ristllin/Nimbus/DISCLAIMER.md

# Disclaimer

Nimbus is a hobbyist, do-it-yourself hardware and firmware project. It is
provided **"as is", without warranty of any kind**, express or implied,
including but not limited to fitness for a particular purpose, merchantability,
and non-infringement. This document supplements, and does not replace, the
warranty and liability disclaimers in [LICENSE](LICENSE) and
[LICENSE-docs](LICENSE-docs).

**By building, modifying, powering, or using a device based on this project,
you accept full and sole responsibility for the result.** The author and
contributors are not liable for any damage, loss, or injury of any kind
arising from the construction or use of hardware or software described here,
including damage to property, data loss, fire, or personal injury.

## Electrical and battery safety

This project describes wiring mains-powered USB supplies, DC-DC converters,
LED loads, and **lithium-ion battery packs (2S 18650)**. Lithium-ion cells can
overheat, vent, catch fire, or explode if they are damaged, short-circuited,
over-charged, over-discharged, punctured, or charged unattended with
inadequate protection.

If you choose to build a battery-powered variant, you do so entirely at your
own risk. At minimum: use quality cells from a reputable supplier, always use
a proper 2S protection/balance board (BMS), fuse the pack, never leave a
charging pack unattended, never exceed component voltage or current ratings,
and stop immediately if anything becomes hot. If you are not comfortable and
experienced with battery wiring, build the USB-powered variant instead, or do
not build the project at all.

## Not a certified product

Devices you build from these files are self-built prototypes, not tested or
certified consumer products. They carry no CE/FCC/UKCA or other regulatory
approval. You are responsible for compliance with all laws, regulations, and
safety standards that apply to you, including those covering radio equipment
(Wi-Fi/Bluetooth), electrical safety, and battery transport and disposal in
your jurisdiction.

## Documentation accuracy

The documentation is provided in good faith and may contain errors or become
outdated. Nothing in it is professional engineering, safety, or legal advice.
Verify everything against your own components before powering anything.
