ristllin/Nimbus/docs/ota.md

# OTA firmware updates

> This page is the OTA design and device-behavior reference. The operator
> runbook - how to cut a release, which tokens expire where and how to renew
> them, and how to rotate the signing key - is maintainer-internal and is not
> part of the public docs.

Nimbus updates itself over Wi-Fi from GitHub Releases. The flash layout was
already A/B (stock `default_16MB.csv`: `otadata` + two 6.5 MB app slots), so OTA
needed no partition change: the running slot downloads the new image into the
**inactive** slot, verifies it, flips the boot flag, restarts - and **rolls back
by itself** if the new firmware can't boot.

⚠ **Delivery is from the dedicated releases repo [`ristllin/nimbus-fw-releases`](https://github.com/ristllin/nimbus-fw-releases), NOT the source repo.** The device
downloads over unauthenticated HTTPS (no repo credentials baked into firmware),
so release assets must live somewhere any device can fetch them - a dedicated,
assets-only public repo (the same pattern as the SFX assets). The signed
binaries carry no secrets, and the ECDSA signature is what devices trust.
Forking the project and shipping to your own devices? See
[`self-hosted-ota.md`](self-hosted-ota.md).

```mermaid
flowchart TD
  TAG["tag vX.Y.Z on Nimbus<br/>(source repo)"] --> CI["release.yml<br/>build nimbus-tft + freenove images<br/>sign typed manifest (ECDSA)<br/>publish images + per-variant web-flash"]
  CI --> REL["Release on nimbus-fw-releases<br/>(PUBLIC delivery repo)"]
  REL -->|"GET /releases/latest/download/manifest.json<br/>302 → objects.githubusercontent.com (followed)"| GET
  subgraph DEV["device (daily / button)"]
    GET["fetch manifest"] --> CMP["compare versions → notify / 1-click install"]
    CMP --> DL["stream .bin → INACTIVE slot (+SHA-256)"]
    DL --> VER["verify SHA + signature<br/>(anchors: include/ota_pubkey.h)"]
    VER --> FLIP["arm NVS guard → flip otadata → restart"]
    FLIP --> OK["healthy 120 s → mark valid ('ok vX')"]
    FLIP --> RB["3 failed boots → flip back ('rollback vX')"]
  end
```

## Trust model

- **Signature** (the real gate): CI signs, per variant, the canonical message
  `nimbus-ota-v2\n<version>\n<type>\n<sha256-hex>\n` with ECDSA P-256
  (secret `OTA_SIGNING_KEY`). The device rebuilds that message from what it
  actually downloaded and verifies against the public keys baked into
  [`include/ota_pubkey.h`](../include/ota_pubkey.h) **before** the boot flag
  flips. Binding version+type kills mix-and-match and cross-version replay. (The
  schema-1 transition is over: `release.yml` publishes only the typed schema-2
  manifest and `parseManifest()` rejects anything else, so the legacy
  `nimbus-ota-v1` message is no longer signed - see Typed manifests.)
- **TLS**: downloads ride `tlsSetup()` (CA-bundle validation, `tlsVerify`
  default ON), so the transport is also authenticated on default settings.
- **Residual**: a MITM against a `tlsVerify=0` device can only replay an old
  *genuinely signed* release; auto-install moves strictly forward in version,
  so the worst case is pinning a device at its current version. Manual
  downgrade needs the authenticated web UI + `force`.
- The `test` variant additionally trusts a COMMITTED test key
  (`test/ota_test_key.pem`, `#ifdef NIMBUS_TEST` only) so the HIL suite can
  sign fixtures. Never flash `env:test` on a production unit.

## Typed manifests (v2)

The manifest is **typed**: `schema: 2`, and each entry in `variants` is keyed on
the device **type**, not the build tag. The four types are frozen:
`nimbus-tft` (the TFT + ring board), and `freenove-28` / `freenove-35` /
`freenove-40` (the all-in-one touchscreen, by panel size). A release publishes one
`manifest.json` holding every type that has an image; a device looks up only its
own type.

```
{ "schema": 2, "version": "v4.3.0", "notes": "...",
  "variants": {
    "nimbus-tft":  { "url": "...", "size": 3600000, "sha256": "...", "sig": "..." },
    "freenove-28": { "url": "...", "size": 3600000, "sha256": "...", "sig": "..." },
    "freenove-35": { ... }, "freenove-40": { ... } } }
```

- **Where the type comes from**: NVS key `otaType`, seeded by the flasher on a
  fresh install or written by the transition release on an existing device. If it
  is unset, the build falls back to its compile-time tag so dev/HIL builds
  (`test`/`test-cyd`) still resolve. A stored type from the wrong board family is
  refused (a Solide build only accepts `nimbus-tft`, a Freenove build only the
  `freenove-*` sizes), so a mis-seeded NVS can never pull a wrong-pinout image -
  the runtime twin of the compile-time board/variant bind in `ota_update.cpp`.
- **Untyped devices get no update**: a device whose type is empty (or absent from
  the manifest) matches no variant and reports "no update" - a settled state, not
  an error. **E-ink devices are frozen this way**: they carry no type, so after
  the transition release they never install again, and the final e-ink image reads
  "Updates have ended for this board."
- **The transition release** is a final **schema-1** manifest published under the
  tag existing firmware polls. Fielded firmware matches it by its build tag
  (`esp32s3`/`cyd`) and installs it; on first boot the new image derives its type
  from `scrModel` + board and persists `otaType`, then uses the schema-2 manifest
  thereafter. Generate it with `tools/make_manifest.py --schema 1`; the typed
  releases use the default `--schema 2`.
- **Derivation only guesses a single-type family.** A Solide + TFT board derives
  `nimbus-tft` (the Solide family has exactly one type). A Freenove has three sizes
  (`freenove-28` / `-35` / `-40`) that board identity cannot tell apart, so an
  UNSEEDED Freenove derives no type and is offered no update: it must be reflashed
  with its explicit size rather than guessing one. The flasher seeds the exact size
  on every real install, so this only ever refuses a Freenove that reached the typed
  scheme with no seed.

The repo-layout decision (reuse `nimbus-fw-releases`, one manifest per release) is
recorded in [`adr/0001-ota-releases-repo.md`](adr/0001-ota-releases-repo.md).

## Cutting a release

Publishing a signed release to the fleet - the version bump and tag, the CI
signing step, the one-time schema-1 transition manifest, the two CI secrets
(`OTA_SIGNING_KEY` and `RELEASE_PAT`), and token/key renewal and rotation - is an
operator task. That runbook is maintainer-internal and is not part of the public
docs. What a device does with a release once it is published is described below.

## Release tags: firmware and Virtual Nimbus image

One release workflow serves two channels, and the tag that is pushed picks the channel.
They are controlled separately: a Virtual Nimbus image can ship without a firmware OTA
release, and no release moves running Virtual Nimbus instances by itself.

| Tag | Example | What it builds and publishes |
|---|---|---|
| OTA tag `vX.Y.Z` (a release candidate adds `-rc`, as in `v4.5.7-rc1`) | `v4.5.7` | the signed firmware OTA release and web-flash images, plus the Virtual Nimbus image `nimbusd:v4.5.7` |
| Virtual tag `vn-vX.Y.Z` or `vn-vX.Y.Z-N` | `vn-v4.5.7-1` | only the Virtual Nimbus image `nimbusd:vn-v4.5.7-1`. No firmware build, no OTA manifest, no web-flash, and no device is offered an update. |

- **Both tags name the current firmware version.** `vX.Y.Z` must equal
  `NIMBUS_FW_VERSION` in `include/version.h`, the version the image reports as `fw` in
  `/api/state`. A tag that names another version, or has neither shape, is refused
  before anything builds.
- **`-N` numbers repeat virtual releases** of one firmware version (`vn-v4.5.7`,
  `vn-v4.5.7-1`, `vn-v4.5.7-2`, ...). The image registry never overwrites an existing
  tag, so every image release needs a new one. `N` is a positive whole number with no
  leading zero.
- **The image tag is the git tag.** The image reports it as `image` in `/api/state`
  (for example `nimbusd:vn-v4.5.7-1`), and the release smoke test checks both `fw` and
  `image` before the image is pushed.
- **Publishing an image does not roll it out.** Which image Virtual Nimbus instances run
  is pinned by the cloud deploy (its `RECONCILER_NIMBUSD_TAG` setting) on either channel.
  Moving instances onto a new image is a separate, deliberate step: point that pin at the
  pushed tag (`v4.5.7` or `vn-v4.5.7-1`) and deploy.
- The tag gate is `tools/release_gate/tag_shape.py`. `python3 -m pytest
  tools/release_gate` tests it and checks that every release job runs only on its
  channel.

## Device behavior

- **Check**: ~2 min after boot, then daily; on demand from Settings → Software
  update on the web page, the device's Settings > Software update menu
  (Orchestrator mode only - "Check for updates" renders "(unavailable)" in
  Notifier mode), or `POST /api/ota/check`. State surfaces in `/api/state`
  (`ota`, `otaResult`, `otaLatest`, `otaNotes`, `otaPct`, `lastOta`, `autoUpd`)
  and `STATUS` (`ota=`, `lastOta=`).
- **A check always ends in a result.** `POST /api/ota/check` returns `202`
  (accepted) or `409` (busy or gated); the verdict then lands in `/api/state`
  as `otaResult`, which a poller can wait on without ever hanging on "checking".
  It settles to exactly one of: `up-to-date` (reached the feed, nothing newer),
  `new-version` (a newer release, with `otaLatest` + `otaNotes`), `unreachable`
  (the release feed could not be reached at all), or `failed` (reached the
  server but the manifest was rejected; `otaErr` carries the short reason).
  `pending` means a check is still running or none has run yet. The distinction
  between `unreachable` and `failed` is honest: a transport failure is never
  reported as "up to date". (`nimbus::ota::checkResult`, host-tested.)
- **The check never blocks the web request, so a tunneled check cannot leak a
  raw 5xx.** `POST /api/ota/check` only *starts* the check. It claims the
  single-flight guard, runs a few cheap local gates (Wi-Fi up, heap headroom),
  hands the manifest fetch and signature verify to a short-lived worker that takes
  the one shared TLS slot, and answers `202 {"ok":true,"state":"checking"}` right
  away. No new long-lived task and no second TLS session are created (the
  concurrency invariants hold). Because the slow HTTPS work runs off the web task,
  the accept lands well inside the relay and origin time budgets, so over the
  encrypted relay tunnel the browser sees that fast `202`, never a raw upstream
  `502` from the edge giving up on a slow origin while the device quietly finishes
  the check. The verdict is read afterwards from `/api/state` (above), and a
  second check pressed while one is in flight is refused (`409 busy`) rather than
  starting a second fetch.
- **On-screen feedback (device menu).** Settings > Software update shows a status
  band while a check or install runs and after it settles, so the check is never
  silent: a progress bar (the download percent while installing, an indeterminate
  "working" block while checking) plus a persistent result line ("Checking for
  updates...", "Up to date - vX", "Update available: vX", or an honest "Update
  check failed (reason)"). The web page's Software update table shows the same
  states. (`nimbus::ota::updateView`, host-tested.)
- **Install**: the web page's **Install Update** button, the device menu's
  Settings > Software update > "Install vX" row (confirm: Cancel / Install and
  restart), Telegram `/update` (owner only), or `POST /api/ota/apply` (`dry=1`
  downloads + verifies without flipping, `force=1` allows same/older AND bypasses
  the battery gate below). During install the
  ring is a theme-color progress bar, the screen says "do not power off", and
  voice capture is refused. The download runs alongside the live Telegram poller
  (heap stays steady; an earlier "stop the poller to free heap" hook is gone - it
  deleted a live queue and crash-rebooted the device).
- **Battery / health gate** (both the manual and the auto path): an interrupted
  flash on a dying pack can leave a slot unbootable, so install is allowed only
  when the pack can finish the write. The rule: **level at or above 40 % AND
  estimated health at or above 60 %, OR the device is on external power, OR
  battery monitoring is disabled** (there is no pack to protect). Below that,
  the refusal names the next step: a low level asks to **Connect power** (`err`
  `need-power`), a low health estimate asks to **Recalibrate to 100 %** (`err`
  `need-recalibrate`, charge full then Calibrate). Because this board has no
  VBUS sense line to prove the charger for itself, every stop offers **Install
  anyway (I am charging)**, which re-submits with `force=1` and skips the gate.
  (`nimbus::ota::installGate`, host-tested.)
- **Auto-install** (`autoUpd`, default OFF): hourly idle-window evaluation -
  no turn/voice in flight, battery ≥50 % or external power, estimated health
  ≥60 % on battery, heap headroom (`nimbus::ota::autoInstallAllowed`,
  host-tested).

## ⚠ Notifier mode: OTA is heap-gated (Orchestrator-mode only, for now)

OTA check/install **refuse with 409 in Notifier mode** and never run there. In
Notifier mode NimBLE owns most of the ~266 KB internal SRAM, leaving ~23 KB free -
below the OTA task-spawn floor (24 KB free internal + 16 KB largest block). The
gate deliberately refuses rather than risk an OOM during the TLS download + flash
write. Consequence: a Notifier-mode device can't self-update over the air; update
it by **USB reflash** or by switching to **Orchestrator mode** (which rests at
~63 KB internal, well above the floor). OTA is fully verified in Orchestrator mode
(Boards 1 & 2). The eventual fix (deferred, owner decision 2026-07-18) is to have
OTA temporarily release BLE during the download in Notifier mode (frees ~40-70 KB
internal), then the post-install restart restores it.
- **Rollback**: before the flip the device arms `otaPend/otaBoots/otaPrev` in
  NVS; `otaupd::bootGuard()` (the FIRST line of `setup()`, raw-NVS so it beats
  every driver) counts boot attempts and flips back to the untouched previous
  slot after 3 failures. Healthy for 120 s (600 s if Wi-Fi never came up) →
  marked valid. Power loss mid-download touches only the inactive slot;
  between guard-arm and flip → disarmed as `aborted-preflip`.

## Update over the USB cable (local, unsigned, cable-gated)

Cloud OTA needs a published signed release, and a fresh ROM esptool flash needs
the physical BOOT button (unreachable over native USB on some units). The USB
serial update is a third path: the **running** firmware accepts a locally-built
`.bin` over the USB cable and installs it through the **same** esp_ota A/B engine,
rollback guard, and deferred reboot as cloud OTA. Compared to cloud OTA it drops
everything that only makes sense for a remotely-fetched signed release: the HTTPS
fetch, the ECDSA signature check, the version-eligibility check, and the
battery/health install gate. It keeps the streamed-sha256 integrity check. The
physical cable is the trust boundary (the same trust model esptool and the ROM
flash rely on), and the operator at the cable owns the power and version decision.
A peer on Wi-Fi cannot reach the serial stream, and a device that is never cabled
has the same trust surface as before.

```
python3 tools/push_firmware.py --port /dev/cu.usbmodemXXXX firmware.bin
```

The host tool opens the port, sends the image size and its sha256, streams the
image in 4 KB chunks each protected by a crc32 (with a per-chunk resend), then
sends the full-image sha256. The device verifies the streamed hash, arms the
rollback guard, flips the boot pointer, and restarts. A corrupt or interrupted
transfer leaves the spare slot untouched and the current firmware running, exactly
like cloud OTA. The device replies are single lines prefixed `NFWU ` so they are
easy to read amid ordinary log output.

- **No auth by default.** The cable is the trust boundary. A backend confirm gate
  exists for anyone who wants to close the "plugged into an untrusted host" case:
  the store flag `usbUpdateConfirm` (default OFF), when ON, makes the device refuse
  a USB update (`err confirm`) until a 60 s window is armed. The gate defaults OFF so
  it never affects the common path. It is controlled from both surfaces: a "Confirm
  USB updates" toggle in the device menu (Settings > Software update) and on the web
  page's Software update panel, plus an "Allow USB update (60s)" action row in that device menu
  (shown only when the toggle is on) that arms the window.
- **Reuse, not a second engine.** The listener calls the same single-flight guard
  as cloud OTA (a USB push refuses `busy` while a background check is running, and
  vice versa) and the same arm-before-flip commit order, so the rollback guarantee
  is identical.
- The listener is compiled into production builds only; the `test` and
  notifier-debug builds keep their own Serial readers.

## Testing

- Host: `pio test -e native -f test_ota_logic` (version/manifest/policy core +
  the signed-message golden, cross-checked against `tools/make_manifest.py
  --print-message`; the battery/health `installGate` branches; the definitive
  `checkResult` mapping incl. reachable-vs-unreachable; and the async check-flow
  class in `test_check_async_lifecycle`: single-flight over every state, so a
  second check while one is in flight can never start a second fetch, and the
  polled verdict is `pending` only until the check settles).
- Host (USB path): `pio test -e native -f test_usbfw_proto` (crc32 vectors, the
  START-header and chunk framing round-trips, and the arm-before-flip commit-order
  sequence, incl. that a failed flip disarms the pending guard).
- HIL: `python3 -m pytest tests/hil/test_ota.py -m net --allow-hardware` -
  local self-signed TLS server (flips `tlsVerify` off/on), test-key-signed
  manifest, real dry-run E2E, sha-fail + sig-fail negatives, 302 redirect hop.
- HIL (release gate): `python3 -m pytest
  tests/hil/test_l29_release_gate.py::TestOtaCheckAnswersFast -m net
  --allow-hardware` times `POST /api/ota/check` over the LAN (must accept in
  under 2 s, off the web task) and polls `/api/state` until `otaResult` is
  definitive. Set `NIMBUS_OTA_MANIFEST_URL` to point the check at a bench manifest
  (else it runs against the real feed). The tunnel property follows from the fast
  LAN answer.
- Rollback drill (console, `env:test`, both slots flashed): `OTASIM arm app0`
  (label from `OTA?` `slot=`) + `OTASIM crash` + `REBOOT` → three synthetic
  crash-boots → device returns on the previous slot with `lastOta=rollback`.
