ristllin/Nimbus/evals/toolcount/README.md

# Tool-count benchmark

A host-side, provider-driven benchmark that measures how the **number of tools
exposed to the model** affects tool-selection accuracy and answer quality. It
complements the on-device orchestrator benchmark one level up (`../README.md`):
that one grades real turns on live hardware; this one isolates a single design
variable - tool exposure - against a provider API, needs no board, and is cheap
to run.

## The question

The device advertises its whole tool registry on every Orchestrator turn (see
`catalog.json` - 49 tools today). Frontier-model guidance says selection accuracy
erodes as that set grows and that schemas bloat the context. This benchmark tests
that claim on our real tool surface and scores three ways of shrinking it.

## The three conditions

For each task the model is given one of three tool surfaces:

| condition | what the model sees | models |
|---|---|---|
| `full` | every catalog tool at once (the current device reality) | the status quo |
| `curated` | only the tools flagged `core` (the ~15-20 target set) | a hand-picked core |
| `lazy` | a few always-on tools + one `search_tools` meta-tool; real tools are revealed only after the model searches for them | progressive disclosure |
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
