ristllin/Nimbus/src/main.cpp

// Nimbus firmware - Notifier mode device.
//
// BLE nsn frames -> decoder -> Mapper -> attention Router -> ring + panel.
// USB serial is power + flashing only, never a status transport (decided
// 2026-07 - see AGENTS.md). The ring is instant (per-job segments / cursor);
// the panel follows on the dwell/coalesce schedule. Encoder rotates a cursor
// over the job list and the detail pane renders after the cursor settles.
//
// P4 wiring lives here now:
//   - boot loads the persisted Config + Mode from NVS/SD (config_nvs), so the
//     profile/overrides survive reboots; a fresh device falls back to defaults.
//   - a LONG-PRESS on the encoder opens the portable SettingsMenu; while it is
//     open, touch drives the menu (rotate/click/long-press gestures) and the panel
//     shows ScreenId::Menu rendered from view(). Any menu mutation applies live
//     (scheduler dwell/coalesce + ring brightness) and persists.
//   - a WiFi AP + captive config portal (src/net) starts in setup(); its save
//     callback persists the same Config and re-syncs the active profile.
// The Notifier BLE path is untouched when the menu is closed: nsn frames keep
// flowing to the ring + panel exactly as before.
//
// Build:  pio run -e esp32s3 -t upload           (silent - clean nsn stream)
//         pio run -e notifierdbg -t upload        (adds a device->host status
//                                                  echo for E2E validation)
#include <Arduino.h>
#include <esp_heap_caps.h>  // heap_caps_calloc (PSRAM-backed mbedTLS allocator)
#include <new>              // placement new (PSRAM-backed panel framebuffers)
#include <esp_bt.h>         // esp_bt_controller_mem_release (free BT RAM in Orch mode)
#include <esp_sleep.h>
#include <esp_task_wdt.h>
#if __has_include(<esp_core_dump.h>)
#include <esp_core_dump.h>   // factory reset erases any crash dump (stacks can hold secrets)
#endif
#include "sys/errlog_fs.h"   // setSuspended - the factory sweep's durable-log barrier
#include <nvs_flash.h>   // nvs_flash_erase() - web factory reset
#include <nvs.h>         // raw NVS read/write to preserve identity across the wipe
#include "agent/agent_config.h"            // AKEY_* frozen NVS key macros
#include "nimbus/config/identity_keys.h"  // keys that must survive a factory reset
#include "nimbus/orch/danger_zone.h"      // CUM-15: device-name keep-list preserved across a reset
#include <mbedtls/platform.h>  // mbedtls_platform_set_calloc_free (route TLS -> PSRAM)
#include <solide/solide.h>

#include "nimbus/power/bright_cap.h"   // 60% LED safety cap (owner feature)

#include "agent/adapters/adapter_factory.h"  // fabricInit
#include "agent/adapters/audio_stt.h"        // Telegram voice-note + voice-input STT
#include "agent/adapters/tts_voices.h"        // live TTS voice catalog (/api/voices)
#include "sys/agent_log.h"                  // alogf -> /api/log ring (voice diag)
#include "agent/memory_subsystem.h"           // setDataFs(SD) - route orch data to the card
#include "agent/files_subsystem.h"            // E1: /mem/files artifact store
#include "agent/orchestrator.h"
#include "nimbus/harness/jobs.h"   // agent::keyFromTag - ring keys derive from session tags (CUM-243 reaper)
#include "agent/loops_subsystem.h"   // Local Loops scheduler (hooks wired below)
#include "agent/dream_subsystem.h"   // DREAMING: reserved nightly maintenance loop
#include "agent/store.h"                      // store::theme()
#include "agent/connectors.h"                 // MCP OAuth pump on the main loop
#include "nimbus/theme.h"                     // themeAccent - LED colour personality
#include "nimbus/status_style.h"              // status -> {theme role, anim} single source
#include "nimbus/voice_flow.h"                // hold-to-talk state machine + error taxonomy (CUM-456)
#include <LittleFS.h>
#include <SD.h>                 // SD card FS (mounted via solide::storage) for orch data
#include <solide/storage.h>     // microSD mount helper
#include <solide/audio.h>                     // long-press-to-talk mic capture
#include <vector>
#include "agent/provider_verify.h"
#include "agent/store.h"
#include "agent/telegram.h"
#include "agent/adapters/audio_tts.h"  // orchSpeakSink - tts device action -> Telegram audio
#include "sys/tls_arbiter.h"
#include "hw/hal_status.h"
#include "hw/tft_out.h"      // colour touch panel (screenModel=tft)
#include "hw/touch_input.h"  // taps -> the same gestures the encoder makes
#include "solide/touch.h"     // hold-to-talk release detection on a touch board
#include "nimbus/touch_cal.h"  // persisted resistive-touch calibration
#include "nimbus/display/screen_model.h"  // absent-vs-explicit scrModel notice rule (CUM-189)
#include "nimbus/display/panel_controller.h"  // scrok / boot panel signal (CUM-388)
#include "nimbus/fault.h"                  // SCREEN fault injection -> scrok=0 (CUM-388)
#include "nimbus_board_flip.h"            // per-board display-flip base (CUM-189)
#include "nimbus/tft_render/menu_tap.h"  // portable tap -> menu-FSM mapping
#include "hw/ring_out.h"
#include "hw/selftest.h"   // device health-check engine + device.* tools + SELFTEST
#include "sys/ota_update.h"   // OTA firmware update (boot guard + check/install)
#include "sys/usb_updater.h"  // USB serial firmware update listener (production-only pump)
#include "modes/notifier_mode.h"
#include "nimbus/attention.h"
#include "nimbus/wifi/copy.h"                  // portable, tested Wi-Fi copy + deviceUrl
#include "nimbus/wifi/setup_ap.h"              // portable, tested setup-AP recovery policy (CUM-190)
#include "nimbus/render_context.h"
#include "nimbus/render_sched.h"
#include "nimbus/signin_codes.h"               // DISPLAY_TTL_MS - the hand-entry code window
#include "hw/power_fuelgauge.h"
#include "hw/power_battery_adc.h"
#include "nimbus/power/power_manager.h"
#include "nimbus/power/battery_model.h"   // battery analytics (time-left, health)
#include "nimbus/power/battery_sense.h"   // honest open-sense-line detector (FIX 3)
#include "nimbus/display/resistive_touch.h"  // resistive touch liveness detector (FIX 4)
#include "nimbus/power/thermal_guard.h"   // LED-load thermal breaker (fried-panel fix)
#include "nimbus/profile.h"
#include "nimbus/ring_plan.h"
#include "nimbus/saver.h"                 // screensaver idle clock (logo after 1 h idle)
#include "nimbus/settings_menu.h"
#include "nimbus_board_power.h"           // explicit per-board battMon default (CUM-202)
#include "nimbus_board_batt.h"            // effective battery divider selection (CUM-370)
#include "nimbus_board_touch_bus.h"       // shared-MISO panel-read hazard (CUM-392)
#include "nimbus_config.h"
#include "version.h"
#include "net/ble_notifier.h"
#include "net/relay_client.h"  // cloud tunnel (cumulo-nimbus)
#include "nimbus/cloud/relay_timing.h"  // kTaskWdtTimeoutMs - single source for the WDT budget
#include "net/webui.h"
#include "net/wifi_portal.h"
#include "net/wifi_store.h"   // the Wi-Fi menu reads saved networks by name
#include "net/wifi_link.h"    // CUM-207: multi-network failover supervisor (step 8)
#include "sfx/sound_fx.h"
#include "nimbus/action_feedback.h"  // menu-action outcome -> feedback cue mapping (host-tested)
#include "sfx/sfx_sync.h"            // sfxsync::statusStr -> device.status sfxSync (W11)
#include "sfx/music.h"              // CUM-40 music player (media.* tools + /play)
#include "nimbus/orch/caps.h"        // spawn capacity constants -> device.status (W11)
#include "nimbus/orch/fetch_policy.h"  // fetchPolicyName -> device.status (W18)
#include "sys/config_nvs.h"
#include "test_console.h"  // no-op inline stubs unless -DNIMBUS_TEST (env:test)
#include <WiFi.h>  // WiFi.onEvent - SFX link sounds (all builds) + F9 reason (test)

using namespace nimbus;

static attn::Router g_router;
static Config g_cfg;
static Selector g_selector;
static ring::Cursor g_cursor;
// Orchestrator voice UX (Phase 4): a cached snapshot of the running sub-sessions
// the encoder cursor moves over. Refreshed once per orch render cycle (not per
// detent - sessionInfos() iterates the journal + heap-allocs). g_cursor.index()
// indexes into this list.
static std::vector<nimbus::orch::SessionInfo> g_sessionList;
// A full-screen Ask-screen override (mode-switch confirmation, voice transcript,
// voice reply). When set, the Ask screen renders it.
static String g_askOverride;
// STICKY reply (P2.3): a reply/voice message on the Ask screen HOLDS until the
// next click (the scheduler is gated while set, like the menu), and the cursor
// pages through it - it used to be overwritten by the next scheduled render
// within seconds ("can't read more than a line or two").
static bool g_askSticky = false;
static int  g_askPage = 0;
// A transient Ask override that precedes a reboot (mode switch): the device
// restarts on its own, so the Ask screen draws NO Close button (it would be dead -
// the reset lands before a tap could reach it). Set true right before rendering
// such a confirmation; a reboot follows immediately, so it never leaks to a later
// dismissible reply (and a fresh boot clears it).
static bool g_askTransient = false;
// Voice hold-to-talk state. g_voiceActive is true while the mic records (drawn as
// the pressed mic; re-entry is guarded by g_voice.canPress()); g_voiceStop is the
// recordToFile stop flag driven by the release watcher; g_voiceDone lets the
// watcher exit. g_voiceReply* carries the async turn reply back from the poll task
// to the main loop for panel rendering.
static volatile bool g_voiceActive = false;
static volatile bool g_voiceStop = false;
static volatile bool g_voiceDone = false;
static volatile bool g_voiceReplyPending = false;
static String        g_voiceReply;
// Hold-to-talk flow (CUM-456): the portable state machine that orders the release
// path (processing is shown BEFORE any network I/O) and holds the processing /
// outcome state until the reply lands. Main-task owned - the touch dispatch,
// captureVoiceTurn() and loop() all run on the loop task - so no lock.
static nimbus::voice::Flow g_voice;
static uint32_t g_voiceEndTarget = 0;            // voice-message count that means OURS is done
static volatile uint32_t g_voiceReleaseMs = 0;   // when the watcher saw the release
// Bench seam timings for VOICE? (release -> first repaint, release -> STT start).
static uint32_t g_voiceShownMs = 0, g_voiceSttMs = 0;
// Theme colors for the voice cue, refreshed on each flow transition (an NVS read -
// the 30 fps ring tick must not pay it).
static solide::ring::RGB g_voiceAccent{0, 0, 0}, g_voiceAlert{0, 0, 0};
// While the voice flow's cue is live (listening, processing, an error outcome) it
// owns the ring: nothing else may recompose over it.
static bool voiceOwnsRing() { return g_voice.ownsRing(); }
// Web chat (POST /api/chat): the turn runs on tg_poll; its reply is captured here
// (chatId "web" in orchSendSink) for GET /api/chat to poll. Single-slot, one owner.
static volatile bool g_webReplyPending = false;
static String        g_webReply;
// Deadline of the web turn currently in flight (0 = none), so GET /api/chat can
// report an HONEST `pending`. Set when a message is accepted, cleared when its
// reply is staged; the deadline is only a backstop for a turn that dies without
// replying (a fan-out head turn may legitimately run for minutes).
static volatile uint32_t g_webTurnDeadlineMs = 0;
static constexpr uint32_t kWebTurnMaxMs = 12UL * 60UL * 1000UL;
// millis() of the last sub-agent start/finish, for the Calm-level ring activity blink
// (set when the session set changes; 0 = no recent activity).
static uint32_t      g_lastActivityMs = 0;
// Screensaver (owner 2026-07-16): after saverMin minutes (NVS, default 60,
// 0 = off) with no activity - knob/button, real job EDGES (broker heartbeat
// re-sends do NOT count), or any non-ambient screen render - the panel swaps
// StatusIdle for ScreenId::Screensaver (the dotted-ring logo + device name).
// Any activity restores live status via saverKick().
static nimbus::SaverTimer g_saver;
static void saverKick();   // defined after renderScreen/g_menu exist
// "Wake the ring" reveal: a single click promotes the ring to the full-brightness
// segment treatment until this deadline (0 = not revealing), so live status is
// glanceable from any posture. compose(reveal=...) reads it via refreshRing().
static uint32_t      g_revealUntilMs = 0;
// Auth-fail Config QR is TRANSIENT: when repeated 401s surface the QR unprompted,
// hold it ~45 s then fall back to StatusIdle. Without this a client that keeps
// polling with a bad token (a stale browser tab) parked the panel on the QR
// forever, so the idle screensaver - which only arms from StatusIdle - never
// showed (owner: "a full night, no logo"). 0 = not currently showing the auth QR.
static uint32_t      g_authQrUntilMs = 0;
static constexpr uint32_t kAuthQrHoldMs = 45000;
// CUM-452: Settings > Connectivity > Wi-Fi > Publish setup network asks loop() to
// put the Setup screen up (the web path raises net::consumeSetupInfoRequest()).
static bool          g_setupInfoReq = false;
// ...and holds it for up to kSetupHoldMs (the sign-in code's own window), ending early
// once Wi-Fi reconnects after the publish took it down. 0 = no hold.
static uint32_t      g_setupHoldUntilMs = 0;
static bool          g_setupHoldSawStaDown = false;
static constexpr uint32_t kSetupHoldMs = 10UL * 60UL * 1000UL;
// CUM-453: the frame on the panel shows the hand-entry sign-in code (a join screen of
// a provisioned device), so loop() repaints it the moment that code stops working.
static bool          g_panelShowsCode = false;
// A frame carrying a freshly minted code was dropped (a blit in flight): the panel
// may still show the previous, dead code, so loop() retries the repaint.
static bool          g_codeFrameDropped = false;
static uint32_t      g_revealDurMs   = 4000;   // actual length of the live reveal window
                                               // (the boot handoff uses a shorter one)
static constexpr uint32_t kRevealMs = 4000;  // how long a single click lights the ring
// Wake reveal is EASED in/out (not snapped): the loop ramps ring brightness over
// these windows while keeping the composed per-segment status colours, so the
// wake breathes on and off gracefully. (leds::setBrightness scales the raw frame.)
static constexpr uint32_t kRevealFadeInMs  = 400;
static constexpr uint32_t kRevealFadeOutMs = 600;
// Boot flourish: a calm breathing-white "I'm coming up" for the first few seconds
// after boot (Pattern::Pulse self-animates), unless a real attention event needs
// the ring first. 0 = not booting. Set at the end of setup().
static uint32_t      g_bootBreatheUntilMs = 0;
static constexpr uint32_t kBootBreatheMs = 2500;
// Theme flourish: picking a theme lights the ring in the new palette for a moment
// so the change is VISIBLE on the main screen. Without it, an idle ring (dark) made
// the pick look like it turned the lights off (owner-reported on the touch board,
// 2026-08-01: "after changing theme the lights seem to be gone"). 0 = not active.
static uint32_t      g_themePreviewUntilMs = 0;
static bool          g_themeFlourishPending = false;  // theme picked -> arm flourish on menu close
static constexpr uint32_t kThemePreviewMs = 2500;
// After a critical-battery deep sleep, wake this often to re-check for a charger
// (the ADC board has no charge-detect pin to wake on - see the shutdownT2 path).
static constexpr uint32_t kLowBattWakeMinutes = 5;

// smoothstep eased 0..256 for x in [0,span] (t^2*(3-2t)); >=span -> 256. Fixed-point.
static uint16_t smoothstep256(uint32_t x, uint32_t span) {
  if (span == 0 || x >= span) return 256;
  const uint32_t t = (x * 256) / span;               // 0..256
  const uint32_t s = (t * t * (768 - 2 * t)) >> 16;  // 256 * smoothstep(t)
  return uint16_t(s > 256 ? 256 : s);
}
// The active ring brightness (RingBrightness param, byte-clamped) - the peak the
// boot breathe + wake-reveal envelope scale within.
static uint8_t ringBrightByte() {
  const int b = g_cfg.effective(Param::RingBrightness);
  return uint8_t(b < 0 ? 0 : (b > 255 ? 255 : b));
}
// Web ring preview (POST /api/preview -> webui's onPreview, fired from loopWeb()
// on the main task). Never touches g_cfg/g_selector: refreshRing() composes from
// a throwaway Config carrying only the previewed profile's presets, so nothing is
// persisted or visible to /api/state. loop() reverts once g_previewUntil passes.
static bool      g_previewActive = false;
static uint32_t  g_previewUntil = 0;
static ProfileId g_previewProfile = ProfileId::Balanced;
// The status the web ring simulator asked to demo (0..5 = solide::ring::Status),
// or -1 = the default two-arc showcase. Lets "Demo on Device" mirror the exact
// status the on-page simulator is showing, not just the theme.
static int       g_previewStatus = -1;
// Posture of the last PLAN actually applied to the ring - diverges from
// g_cfg.posture() while a preview is live; RENDER? must report what the ring shows.
static uint8_t   g_lastPosture = 0;
// P3: end of the web-action LED confirmation Flash window (0 = none active).
// Set when a save/scan confirm blips the ring; the loop restores the composed
// ring (refreshRing) when it expires.
static uint32_t      g_ledConfirmUntilMs = 0;

// A transient one-line action confirmation shown in the menu help pane (the
// "when the panel is alive" channel for a menu-action outcome). Empty/expired =
// the pane shows its normal help text. The ring swell + sound carry the same
// outcome on the channels that survive a dead panel.
static std::string   g_menuToast;
static uint32_t      g_menuToastUntilMs = 0;

// Orchestrator device-action overrides (DeviceSink; staged on the poll task under
// the config lock, applied by the main loop). "lights off" darkens the ring until
// lights:full, a user click (reveal), or a NEW attention event re-lights it - an
// owner-silenced ring must not swallow a call-to-action. A `led` action paints an
// explicit pattern that owns the ring until a lights action or click clears it.
static volatile bool g_lightsOff = false;
static volatile bool g_ledOverrideActive = false;
static uint8_t  g_ledOvMode = 0, g_ledOvR = 0, g_ledOvG = 120, g_ledOvB = 255, g_ledOvBright = 128;
static bool     g_ledOvHasBright = false;
static volatile bool g_devActDirty = false;  // loop: apply the staged override state
// Expiry for a MODEL-painted `led` pattern (millis deadline; 0 = no expiry). Set
// by the device sink from the per-mode AttnHoldMs; the battery-drain pin leaves it
// 0 on purpose - a measurement load must hold for hours, decoration must not.
static volatile uint32_t g_ledOvUntilMs = 0;

// Hard ceiling on the Calm "thinking" breathe (orchWorking = turnInFlight). The
// stuck-turn reaper already frees a hung turn (~loop deadline + 2 min), but as an
// absolute belt-and-suspenders - so the ring can NEVER breathe "working" for hours
// if that reaper is ever wedged - the watchdog latches this past kWorkingHardMaxMs
// of continuous turnInFlight, and compose() then drops the breathe. Cleared the
// instant turnInFlight goes false (the reaper or a clean turn-end).
static volatile bool g_workingCeilingHit = false;

// Battery drain / storage (battery-measurement). A high, constant LED load (solid white)
// is pinned via the SAME g_ledOverrideActive latch the `led` action uses, so refreshRing()
// + tickAnimation() release the ring and Pattern::Solid holds with no maintenance. A
// separate g_highLoadActive marks it as a BATTERY op so attention/refresh can't reclaim
// the ring mid-run, and the settle state machine periodically drops the ring for a few
// seconds to read a NEAR-RESTING voltage - under ~2 A the pack sags ~0.4 V/cell, so raw
// under-load voltage can't calibrate the resting liIonPercent table. DRAIN is TEST-only
// (campaign, runs to cutoff); STORAGE is a production user feature (drain to ~70% + hold).
static volatile bool     g_highLoadActive  = false;  // drain OR storage pinning the ring
static volatile bool     g_drainDeep       = false;  // DRAIN deep: suppress T2 -> run to cutoff
static volatile uint16_t g_storageTargetMv = 0;      // STORAGE stop (pack mV); 0 = campaign drain
static volatile bool     g_hlSettling      = false;  // in a load-off settle window
static uint32_t          g_hlLastSettleMs  = 0;
static uint32_t          g_hlSettleStartMs = 0;
static volatile uint16_t g_hlRestingMv     = 0;      // last load-off resting pack mV (0 = none yet)
static uint32_t          g_hlRestingAtMs   = 0;
// HOST DEAD-MAN (battlab). A host-driven campaign drain is armed by a host process
// that MUST keep refreshing it. If that host dies/restarts/sleeps or the network
// drops, NOTHING else stops the ~1.5 A load and the pack runs FLAT - that happened
// live (2026-07-16: a lab restart orphaned a 45 % drained-mode run; it drained ~26
// min unsupervised and killed the pack). The device must fail safe on its own.
// Rollover-correct by construction: store the last-refresh stamp and compare an
// UNSIGNED difference (same idiom as the settle machine), never `now > deadline`.
// 0 ttl = disarmed (a human at the console, and STORAGE which auto-stops itself).
static volatile uint32_t g_drainRefreshedMs = 0;     // millis() of last arm/refresh
static volatile uint32_t g_drainTtlMs       = 0;     // 0 = dead-man DISARMED
static constexpr uint32_t kDrainTtlDefaultS = 120;   // host must refresh within this
static constexpr uint32_t kDrainTtlMaxS     = 900;   // 15 min hard ceiling
static constexpr uint8_t  kDrainBright        = 150;              // DEFAULT + RECOMMENDED max
                                                                  // (~1.5 A on the 45-LED ring). WAS
                                                                  // 190 (~2 A) - that fried an e-ink
                                                                  // panel in ~15 min (2026-07-15).
// The web `bright=` param may now request the FULL scale (up to 255) so the lab
// can characterize at higher loads, but that is above the recommended ceiling and
// the caller is warned. The runtime protection is the THERMAL GUARD below (trips
// the load at 65 °C / +18 °C rise) + the host max-temp stop - NOT a fixed clamp.
static constexpr uint8_t  kDrainBrightHardMax = 255;
static constexpr uint32_t kHlSettleIntervalMs = 15u * 60u * 1000u;
static constexpr uint32_t kHlSettleMs         = 9000;            // load-off relax window

// THERMAL GUARD (fried-panel incident 2026-07-15: ~10 W of white LEDs beside the
// SSD1680 killed a screen in ~15 min - and nothing was even reading the die
// sensor, so there is no record of how hot it got). The S3's internal DIE sensor
// is the only thermometer on this hardware; nimbus::power::ThermalGuard (pure,
// host-tested) trips on an absolute ceiling OR a rise-over-baseline delta:
//   Trip   -> LED load OFF, cool;   Resume (hysteresis) -> reduced brightness;
//   Abort (>3 trips) -> the drain/storage op is cancelled outright.
// A separate GLOBAL backstop kills ANY ring output at kGlobalLedKillC, so a
// model-driven `led` pattern can't cook the panel either.
static nimbus::power::ThermalGuard g_thermal;
static volatile float g_dieTempC = 0.0f;        // latest die reading (/api/state)
static uint32_t       g_thermTickMs = 0;        // 2 s poll gate
static volatile bool  g_thermalAbortLatch = false;  // op cancelled by heat (surfaced)
static constexpr uint8_t kDrainBrightReduced = 110;  // post-trip resume level (~1.1 A)
static constexpr float   kGlobalLedKillC     = 70.0f;
// battlab: the ACTIVE per-run LED load (web `bright=` param, clamped in drainSet;
// defaults to kDrainBright). Surfaced as drainBright in /api/state.
static uint8_t g_drainBright = kDrainBright;
// Guard-appropriate high-load brightness: off while tripped; reduced after any trip;
// never above the per-run load.
static uint8_t hlBright() {
  if (g_thermal.tripped()) return 0;
  const uint8_t base = g_drainBright;
  return g_thermal.trips() > 0 ? (kDrainBrightReduced < base ? kDrainBrightReduced : base)
                               : base;
}

// Talk-to-configure staging (DeviceSink Config knobs; poll task -> main loop).
// -1 = not staged. Theme is a short slug (bounded copy under the lock).
static int16_t  g_cfgPendPosture = -1;
static int16_t  g_cfgPendProfile = -1;
static int32_t  g_cfgPendAttnHold = -1;
static char     g_cfgPendTheme[16] = {0};
static volatile bool g_cfgPendDirty = false;

// Deferred reboot: web-layer mode changes (AsyncTCP task) and the orchestrator's
// `reboot` device action (poll task) can't call ESP.restart() inline; they set
// this and loop() (main task) reboots at a clean point.
static volatile bool g_rebootPending = false;
static volatile int  g_modeSwitchTo = -1;   // >=0: the pending reboot is a web mode switch
                                            // (target mode) -> show the same confirm UX as the menu
static volatile bool g_factoryResetPending = false;  // web factory-reset: erase NVS + reboot on main task
static volatile bool g_factoryEraseSd = false;       // CUM-15: also erase /mem in the factory-reset flow
static volatile bool g_sdResetPending = false;       // web SD reset: erase /mem durable store + reboot
static volatile bool g_sdFormatPending = false;      // CUM-15: web full-card format (reformat whole SD) + reboot
static volatile bool g_powerOffPending = false;      // CUM-224: web power-off -> clean shutdown + deep sleep on main task
static render::Scheduler g_sched;
static NotifierMode g_notifier(g_router);
static SettingsMenu g_menu(g_cfg);

// The panel currently on the panel - always compiled: the loop's header-
// glyph change-detector gates its repaint on "is StatusIdle live?" (below), so
// production needs this too. Set by renderScreen()/renderMenu().
static volatile uint8_t g_lastScreen = uint8_t(attn::ScreenId::StatusIdle);

// First-run auto-return to Setup (CUM-259). While a credless device is parked on
// StatusIdle, this holds the millis() deadline at which the loop repaints SetupInfo;
// 0 = disarmed. Armed in renderScreen(StatusIdle) when deviceNeedsSetup(), re-armed
// on touch, disarmed by any other render. ~30 s: long enough not to yank the screen
// out from under a reading owner, short enough that nobody sits stranded.
static uint32_t g_setupReturnAtMs = 0;
static constexpr uint32_t kSetupReturnMs = 30000;

// An AMBIENT (non-attention) screen intent must NOT repaint over the long-idle
// screensaver logo. When the logo is up, the broker's ~30 s snapshot heartbeats
// still emit a StatusIdle screen intent; repainting it under the logo makes the
// screensaver entry re-fire, and each StatusIdle<->Screensaver swap is a ~2.2 s
// FastBW invert flash (owner: "the standby logo keeps flashing"). A CTA
// (attention) still renders - it wakes the panel because a job needs the owner -
// and a genuine job edge calls saverKick() -> StatusIdle first, so real activity
// is never dropped. This gates ONLY the ambient heartbeats while the logo shows.
static inline bool screenAmbientAllowedOverSaver(bool attention) {
  return attention || g_lastScreen != uint8_t(attn::ScreenId::Screensaver);
}
#ifdef NIMBUS_TEST
// Render-state snapshot for the test console (RENDER? / onRender emit, F2/F4).
// Written by renderScreen()/renderMenu()/refreshRing() below and read by the
// tc:: hooks. Guarded so production (esp32s3) carries only the one screen byte.
static volatile int     g_lastSeg = 0;
static volatile bool    g_lastSingle = false;
static volatile bool    g_lastDark = true;
static volatile uint8_t g_lastBright = 0;
#endif

// ---- Battery / power (plan P6) ---------------------------------------------
// No battery hardware exists on the board yet (solide-drivers v0.1.0 ships
// none), so the default monitor is NullMonitor: every sample is invalid, the
// policy never fires, and the device runs as desk-powered with the battery UI
// hidden. Define NIMBUS_HAS_FUEL_GAUGE (and verify the pins in nimbus_config.h)
// to compile in the MAX17048 impl and drive the real thresholds.
#if defined(NIMBUS_HAS_FUEL_GAUGE)
static hw::FuelGaugeMonitor g_fuelgauge;
static power::Monitor* g_monitor = &g_fuelgauge;
#elif defined(NIMBUS_HAS_BATTERY_ADC)
static hw::AdcBatteryMonitor g_battAdc;   // resistor-divider ADC sense (no fuel-gauge chip)
static power::Monitor* g_monitor = &g_battAdc;
#else
static power::NullMonitor g_nullPower;
static power::Monitor* g_monitor = &g_nullPower;
#endif
static power::Manager g_power(
    g_monitor, &g_selector,
    power::PolicyConfig{NIMBUS_BATT_T1_PCT, NIMBUS_BATT_T2_PCT,
                        NIMBUS_BATT_HYST_PCT, NIMBUS_VBUS_DEBOUNCE_MS});
static uint32_t g_lastPowerTick = 0;

// Battery analytics: turns the raw Sample stream into time-to-empty + health +
// a self-improving discharge rate (nimbus::power::BatteryModel, host-tested).
// Sampled on each telemetryDue edge; learned state persists to NVS so accuracy
// carries across reboots. g_battEstimate is a POD snapshot the web layer reads.
// Cells comes from the board map (the Freenove is 1S, the Solide 2S), not a
// compile constant - a wrong cell count makes the per-cell SoC read a 1S pack as
// a half-charged 2S one (pinned at 0%). board() is constexpr-initialized, so it is
// safe to read here at static-init time.
static nimbus::power::BatteryModel   g_battModel(solide::board().batt.cells);
static nimbus::power::BatteryEstimate g_battEstimate;
// Honest open-sense-line detector (FIX 3): fed (monitoringOn, sample.valid) on each
// telemetry tick; its debounced verdict is surfaced as batt.senseMissing + a health
// row so an open sense divider is not silently shown as "desk-powered". The claim
// is evidence-gated (battery_sense.h): it needs proof a pack once worked - a valid
// sample this boot, or the persisted anchor loadBattModel() seeds - so a solide
// board legitimately used desk-powered with no pack (monitoring defaults ON there)
// keeps its honest "no gauge (desk-powered)" row instead of a false alarm.
static nimbus::power::SenseMissingDetector g_senseMissing;
// Resistive (XPT2046) touch liveness (FIX 4): fed one solide::touch::readRaw per
// low-cadence poll; trips only on the persistent stuck-high (all-4095) dead
// signature so touch{} and the health row stop reporting a dead panel as "ok".
static nimbus::display::ResistiveTouchLiveness g_touchLiveness;
static uint32_t g_lastTouchLivenessMs = 0;

// Diagnostic toggles for the CUM-392 A/B (driven only by the test-console PROBES /
// BUSLOAD hooks; those hooks compile to nothing in production, so these stay at
// their defaults there). g_fix4Enabled gates the resistive touch-liveness poll so
// PROBES can silence every v4.5.0-added poller for a clean baseline; g_busLoad
// forces a repaint every loop so a diagnostic can run under worst-case bus traffic.
static bool g_fix4Enabled = true;
static bool g_busLoad = false;

// Battery hardware from the board map. cells never 0 (both boards set it); the
// divider is owner-tuned on hand-built boards (resistors vary) but fixed on an
// all-in-one. The fixed-vs-tunable choice lives in nimbus_board_batt.h so the ADC
// begin() here and /api/state in webui.cpp report the SAME divider (CUM-370).
static uint8_t  battCells()  { if (uint8_t o = agent::store::battCellsOvr()) return o; const uint8_t c = solide::board().batt.cells; return c ? c : uint8_t(NIMBUS_BATT_CELLS); }
static int      battAdcPin() { return solide::board().batt.sense >= 0 ? int(solide::board().batt.sense) : int(NIMBUS_BATT_SENSE_PIN); }
static uint16_t battDivX100() { return nimbus::effectiveBattDivX100(agent::store::battDividerX100()); }
// Battery monitoring on/off. A hand-built board (Solide S3) ships WITH a pack, so
// monitoring defaults ON; an all-in-one desk board (Freenove CYD) treats a battery as
// an add-on, so it defaults OFF (opt-in) - otherwise the floating ADC reads "empty"
// and the device sleeps with no pack fitted. The owner can opt in (web Settings). The
// default is an EXPLICIT per-board field (nimbus_board_power.h), not the old
// epd.sck>=0 e-ink proxy that would silently flip if the deprecated epd pins were
// cleaned out of the board table (CUM-202).
static bool battMonOn() { return agent::store::battMon(nimbus::battMonDefaultForThisBoard()); }
static uint16_t g_battSavedSegments = 0xFFFF;   // last-persisted segment count (persist on change)
// Low-battery ping gate (field 2026-08-11: the T1 edge re-fires on every wake-
// sniff boot; the ping needs its own persisted memory). Loaded in setup().
static nimbus::power::AlertGate g_lowBattGate;
static uint32_t g_lowBattSavedPingEp = 0;
static uint16_t g_battSavedAnchor   = 0xFFFF;   // last-persisted full anchor mV (persist on change)

// Apply the owner's battery chemistry + cell count + optional custom SoC curve to
// the model. Defaults (chemistry "liion", board cells, no custom curve) reproduce
// the shipped behaviour exactly. Called at boot and after a live config change.
static void applyBattChemConfig() {
  g_battModel.setChemistry(nimbus::power::chemistryFromSlug(agent::store::battChem().c_str()));
  g_battModel.setCells(battCells());
  String cv = agent::store::battCurve();
  nimbus::power::LiIonCurvePoint pts[nimbus::power::kMaxCurvePoints];
  int n = cv.length() ? nimbus::power::parseCurveCsv(cv.c_str(), pts, nimbus::power::kMaxCurvePoints) : 0;
  if (n >= 2) g_battModel.setCustomCurve(pts, n);
  else        g_battModel.clearCustomCurve();
}

// Serialize/parse BatteryModelState as a compact CSV in one NVS key.
static void loadBattModel() {
  String csv = agent::store::batteryModelState();
  if (!csv.length()) return;
  nimbus::power::BatteryModelState st;
  // "learnedRate,segments,baselineMs,health[,fullAnchorCellMv[,baselineRuntimeSec]]"
  // - the trailing fields are optional for forward-compat with older blobs (anchor
  // landed with top-end calibration; runtime baseline with battery-measurement).
  int a = csv.indexOf(','), b = csv.indexOf(',', a + 1), c = csv.indexOf(',', b + 1);
  if (a < 0 || b < 0 || c < 0) return;
  int d = csv.indexOf(',', c + 1);
  int e = d < 0 ? -1 : csv.indexOf(',', d + 1);
  st.learnedRatePctPerHr = csv.substring(0, a).toFloat();
  st.segments = (uint16_t)csv.substring(a + 1, b).toInt();
  st.baselineBandMs = (uint32_t)csv.substring(b + 1, c).toInt();
  st.healthPct = (uint8_t)csv.substring(c + 1, d < 0 ? csv.length() : d).toInt();
  if (d >= 0)
    st.fullAnchorCellMv = (uint16_t)csv.substring(d + 1, e < 0 ? csv.length() : e).toInt();
  if (e >= 0) st.baselineRuntimeSec = (uint32_t)csv.substring(e + 1).toInt();
  g_battModel.load(st);
  g_battSavedSegments = st.segments;
  g_battSavedAnchor   = st.fullAnchorCellMv;
  // Durable pack evidence for the open-sense claim (battery_sense.h): a persisted
  // full-charge anchor or completed discharge segment is reachable ONLY through
  // valid samples (classifyTrend and the segment path both gate on Sample.valid),
  // so either one proves a pack once worked on this unit. Seed the detector so an
  // invalid streak after such history is reported as the fault it is; a unit with
  // no such history keeps the honest "no gauge (desk-powered)" row. baselineRuntimeSec
  // is deliberately NOT evidence - the drain-campaign tooling can seed it.
  if (st.fullAnchorCellMv != 0 || st.segments != 0) g_senseMissing.seedEverSawValid();
}
static void saveBattModel() {
  nimbus::power::BatteryModelState st = g_battModel.save();
  char buf[88];
  snprintf(buf, sizeof buf, "%.3f,%u,%lu,%u,%u,%lu", st.learnedRatePctPerHr,
           (unsigned)st.segments, (unsigned long)st.baselineBandMs, (unsigned)st.healthPct,
           (unsigned)st.fullAnchorCellMv, (unsigned long)st.baselineRuntimeSec);
  agent::store::setBatteryModelState(String(buf));
  g_battSavedSegments = st.segments;
  g_battSavedAnchor   = st.fullAnchorCellMv;
}

// ---- Orchestrator mode state (plan §3.6) -----------------------------------
// The orchestrator turn loop + Telegram poll run on their own FreeRTOS task
// (tg_poll, spawned by telegram::begin). Sub-session states flow OUT via the
// EventSink onto the SAME attn::Router the Notifier feeds, so the ring + panel
// render sub-agent jobs exactly like nsn jobs. The sink runs on the poll task
// while the main loop reads g_router on the main task, so the two are serialized
// with the same net::ConfigLockGuard the menu/web layer already uses; a flag
// tells the main loop to recompose the ring + queue an screen intent.
static agent::HeavyFabric g_fabric;
static bool          g_orchMode = false;       // resolved once at boot
// The color touch panel is the only supported display (e-ink removed in v4.4).
// True once it is up; flips false only in the fail-soft path when panel bring-up
// fails, which gates rendering off so a dead panel cannot stall the device.
static bool          g_screenIsTft = false;
// First-run touch calibration GATE (CUM-189 / CUM-245): armed at boot when a freshly
// flashed board has no stored per-unit cal AND its touch class needs the guided step
// (resistive panels drift per unit; capacitive ones skip - firstRunCalPolicy decides).
// While the gate is active the guided TouchCal flow (serviceCalGate) is the ONLY
// surface that consumes touch - no tap reaches UI navigation - so a fresh resistive
// panel's approximate/phantom uncalibrated taps can never self-navigate. Cal FIRST,
// then the normal first-run flow. The gate opens the instant a cal is stored (a
// completed solve, or a deliberate long-press skip); a capacitive panel is never gated.
static bool          g_calGateActive = false;
static nimbus::touch::TouchKind g_firstRunTouchKind = nimbus::touch::TouchKind::Resistive;
// The gated flow's state: the pure four-corner wizard, the deliberate-skip recognizer,
// and the raw press-edge tracking that feeds them (uncalibrated, so read raw ADC, not
// the calibrated poll()). g_calGateSig is the last-painted (step, countdown) signature,
// so the TouchCal surface repaints only when it actually changes.
static nimbus::touch::CalWizard g_calWiz;
static nimbus::touch::SkipHold  g_calSkip;
static bool          g_calGateWasDown = false;   // debounced down-state last poll (edge detect)
static uint8_t       g_calGateDownRun = 0, g_calGateUpRun = 0;  // raw-chatter debounce runs
static uint16_t      g_calGateLastX = 0, g_calGateLastY = 0;    // last VALID raw press coords
static uint32_t      g_calGateLastPollMs = 0;    // ~50 Hz raw-read rate limit (bus-friendly)
static int32_t       g_calGateSig = INT32_MIN;
#ifdef NIMBUS_TEST
// CALGATE console seam (CUM-245), defined after serviceCalGate/persistCalAndReleaseGate.
static String firstRunCalGateConsole(int op);
#endif
// True when the stored scrModel is not "tft" (a stale "eink" unit; frozen NVS key).
// We run the color panel regardless and hold a clear "unsupported display" notice on
// it at the end of setup (see the boot-notice block).
static bool          g_unsupportedScreenModel = false;
// White-screen mitigation (TFT): drop the SoftAP once STA is up so its continuous
// beacon TX stops disturbing the panel; bring it BACK when STA goes down so the
// setup/recovery web page is always reachable when Wi-Fi is unavailable. Set in
// the WiFi events, drained in loop() (the mode change must run on the main task).
static volatile bool g_dropApPending = false;
static volatile bool g_restoreApPending = false;
// A fresh TFT needs a bounded AP+STA overlap so its browser can carry the auth
// token to the new LAN origin. Normal boot/reconnect still drops immediately;
// only /savewifi arms this window, and /api/wifi/handoff shortens it once the
// browser has safely received the destination.
static volatile bool g_apHandoffArmed = false;
static volatile uint32_t g_dropApAfterMs = 0;
static uint32_t      g_lastApReconcileMs = 0;  // periodic AP<->STA reconcile (self-heal)
static solide::BeginResult g_hal{};            // per-subsystem HAL health from solide::begin()
static bool          g_bootPanelSignaled = false;  // one-shot boot panel signal fired (CUM-388)

// Can this board maintain a real panel-liveness verdict (CUM-423)? False on a
// shared-MISO solide board, where the render-independent RDDST poll is gated off to
// keep touch alive (CUM-392): the panel binds but nothing feeds the verdict. The
// ONE definition, so panelScrok(), the boot beacon, and the health-row hook can
// never disagree about which boards are self-checkable.
static bool panelLivenessKnown() {
  return !(g_screenIsTft && hw::tft::panelReadbackGated());
}

// The live tri-state "screen confirmed up and answering" verdict (CUM-388/423):
// the ONE source the STATUS scrok field and the boot panel signal both read, so
// they can never drift from each other or from the health "screen" row. Yes only
// when the panel bound at boot AND is not fault-injected absent AND the debounced
// controller-liveness verdict is not "not responding" AND liveness is knowable on
// this board. A wrong-variant flash binds the panel blindly but the controller
// never answers, so this reads No. On a shared-MISO solide board the liveness poll
// is gated off to protect touch (CUM-392), so there is no render-independent feed:
// the verdict is Unknown (honest "cannot self-check"), never a false Yes.
static nimbus::display::Scrok panelScrok() {
  return nimbus::display::screenScrok(
      /*boundOk=*/g_hal.display,
      /*faultInjected=*/nimbus::fault::active(nimbus::fault::SCREEN),
      /*notResponding=*/g_screenIsTft && hw::tft::controllerNotResponding(),
      /*livenessKnown=*/panelLivenessKnown());
}

// One-shot boot panel signal (CUM-388). Twice a Freenove got the Solide image
// (wrong display pinout): it boots network-healthy with a black screen and nobody
// notices ("it's online"). The firmware already knows (the debounced
// controllerNotResponding() verdict), but that lived only in the health payload,
// which a flasher checking "network online" never sees. So emit it to serial ONCE
// at boot: a loud, unmissable line a human watching the port cannot miss, plus a
// machine token (PANEL scrok=<0|1>) tools/setup_device.py greps to fail a dead-
// panel flash instead of printing "installed" over black glass. Production path
// (not NIMBUS_TEST-gated): this is the device's own boot beacon, not a test hook.
static void emitBootPanelSignalOnce(uint32_t now) {
  if (g_bootPanelSignaled) return;
  using nimbus::display::BootPanelSignal;
  const BootPanelSignal sig = nimbus::display::bootPanelSignal(
      /*boundOk=*/g_hal.display,
      /*notResponding=*/g_screenIsTft && hw::tft::controllerNotResponding(),
      /*livenessKnown=*/panelLivenessKnown());
  switch (sig) {
    case BootPanelSignal::Responding:
      // Give the debounced verdict (~6 s: threshold 3 at the 2 s cadence) time to
      // latch before making a POSITIVE claim, so a dead panel that has not tripped
      // yet is never labelled up. A dead panel latches first and takes the branch
      // below well before this window.
      if (now < 12000) return;
      Serial.println("PANEL scrok=1");
      break;
    case BootPanelSignal::Unverifiable:
      // Shared-MISO solide board (CUM-423): the render-independent liveness poll is
      // gated off to keep touch alive, so the panel's liveness cannot be self-checked.
      // Report it honestly as unknown, never a false scrok=1, and tell the operator
      // the one thing that settles it: look at the glass. Wait the same settle window
      // as the healthy beacon so a freshly-attached monitor and the installer catch it.
      if (now < 12000) return;
      Serial.println("?? DISPLAY LIVENESS UNKNOWN on this board; touch shares the "
                     "panel bus, so it cannot self-check. Look at the screen.");
      Serial.println("PANEL scrok=unknown");
      break;
    case BootPanelSignal::NotResponding:
      // Bound at boot but the controller never answers: the wrong-variant-flash
      // signature. Reachable only after the debounce latches, so no time gate.
      Serial.println("!! DISPLAY NOT RESPONDING - likely the WRONG board variant "
                     "was flashed; reflash via tools/setup_device.py");
      Serial.println("PANEL scrok=0");
      break;
    case BootPanelSignal::InitFailed:
      // begin() failed outright: surfaced honestly, but as a hint (a dead panel OR
      // a wrong variant), never a hard variant claim. Known at boot; wait a moment
      // so a freshly-attached serial monitor catches the line.
      if (now < 2000) return;
      Serial.println("!! DISPLAY DID NOT COME UP - panel init failed; check the "
                     "display or reflash via tools/setup_device.py");
      Serial.println("PANEL scrok=0");
      break;
  }
  Serial.flush();
  g_bootPanelSignaled = true;
}
static bool          g_bleEnabled = true;       // Connectivity > Bluetooth (NVS, runtime)
static volatile bool g_orchRingDirty = false;  // set by the sink, drained by loop()
static volatile bool g_orchScreenRender = false;  // an attention event wants the panel
static volatile bool g_saverRestoreReq = false; // saverKick wants the screensaver
                                                // painted over with live status; the
                                                // RENDER is deferred to loop() because
                                                // saverKick fires from the event tap on
                                                // the tg_poll turn task (crash, below)
static volatile uint8_t g_orchScreenId = uint8_t(attn::ScreenId::StatusIdle);
static volatile bool g_orchScreenAttn = false;

// EventSink: route a sub-session event into the attention Router (poll task).
// Held under the net config lock so /api/state and the main loop never read a
// torn job table. Stashes the fan-out for the main loop to act on.
// SFX event tap: installed on the shared router, so EVERY attention event -
// notifier BLE feed, orchestrator sink, battery policy - reaches the sound
// engine through one seam. JobState goes through per-key edge detection (a
// broker re-sends frames; repeats must not re-voice); the rest map 1:1. All
// gating (per-mode level rank, rate limit, speaker fault, voice mute) happens
// inside sfx::fire - this stays a cheap dispatch.
static void sfxEventTap(const attn::Event& e) {
  using nimbus::sfx::Ev;
  switch (e.type) {
    case attn::Event::Type::JobState:
      // onJobState's per-key edge table separates real edges from the broker's
      // snapshot heartbeats; only a real edge counts as screensaver activity.
      if (::sfx::onJobState(e.key, e.status)) saverKick();
      break;
    case attn::Event::Type::IncomingAsk: ::sfx::fire(Ev::NeedsYou); saverKick(); break;
    case attn::Event::Type::AskCleared:  ::sfx::fire(Ev::AskCleared); saverKick(); break;
    case attn::Event::Type::LowBattery:  ::sfx::fire(Ev::LowBattery); break;
    case attn::Event::Type::BatteryOk:   ::sfx::fire(Ev::BatteryOk); break;
    case attn::Event::Type::NetworkDegraded: ::sfx::fire(Ev::NetDegraded); break;
    case attn::Event::Type::NetworkOk:   ::sfx::fire(Ev::NetOk); break;
    default: break;   // JobProgress / Voice: never voiced from the tap
  }
}

static void orchEventSink(const attn::Event& e) {
  net::ConfigLockGuard lk;
  // A NEW call-to-action overrides a silenced OR model-painted ring: neither
  // "lights off" nor a decorative led pattern may swallow a needs-you/error cue
  // (safety over silence). Ambient events respect both.
  if ((g_lightsOff || g_ledOverrideActive) && !g_highLoadActive &&
      e.type == attn::Event::Type::JobState &&
      e.status <= uint8_t(solide::ring::Status::Offline) &&
      attn::isAttentionStatus(solide::ring::Status(e.status))) {
    g_lightsOff = false;
    g_ledOverrideActive = false;
    g_devActDirty = true;
  }
  const attn::Decision d = g_router.route(e, millis());
  if (d.ringDirty) g_orchRingDirty = true;
  if (d.screen.render) {
    g_orchScreenRender = true;
    g_orchScreenId = uint8_t(d.screen.id);
    g_orchScreenAttn = d.screen.attention;
  }
}

// DeviceSink: execute a VALIDATED led/lights/reboot action from the orchestrator
// (poll task). Only STAGES state under the lock; the main loop owns the LEDs and
// applies it (g_devActDirty), so the poll task never races tickAnimation.
static void orchDeviceSink(const nimbus::orch::ValidatedAction& a) {
  using nimbus::orch::ActionKind;
  if (a.kind == ActionKind::Reboot) { g_rebootPending = true; return; }
  net::ConfigLockGuard lk;
  if (a.kind == ActionKind::Lights) {
    agent::alogf("devsink: lights -> %s", a.lightsOff ? "off" : "full");
    g_lightsOff = a.lightsOff;
    g_ledOverrideActive = false;         // a lights action clears any led pattern
    g_devActDirty = true;
  } else if (a.kind == ActionKind::Led) {
    g_ledOverrideActive = true;
    g_lightsOff = false;
    g_ledOvMode = uint8_t(a.mode);
    g_ledOvR = a.r; g_ledOvG = a.g; g_ledOvB = a.b;
    g_ledOvHasBright = a.hasBrightness;
    g_ledOvBright = a.brightness;
    // A model-painted pattern is decoration, not a call-to-action - bound it to
    // the SAME per-mode hold a real CTA gets (Full 5 min / Balanced 2 / Dark 1,
    // owner-customizable). Without this a single turn's `led` action owned the
    // ring FOREVER (no TTL; the only clear was a new attention event) - the
    // field report was a rainbow breathing at full brightness for hours.
    g_ledOvUntilMs = millis() +
                     uint32_t(g_cfg.effective(nimbus::Param::AttnHoldMs));
    g_devActDirty = true;
  } else if (a.kind == ActionKind::Config) {
    // Talk-to-configure: stage the validated knobs; the main loop applies them
    // through the SAME pipeline as the menu/web UI (g_cfg + applyConfig +
    // persistConfig), so a spoken "go full" behaves exactly like a tap.
    if (a.hasPosture)    g_cfgPendPosture = a.posture;
    if (a.hasProfile)    g_cfgPendProfile = a.profile;
    if (a.hasAttnHoldMs) g_cfgPendAttnHold = a.attnHoldMs;
    if (a.hasTheme) {
      strncpy(g_cfgPendTheme, a.theme.c_str(), sizeof(g_cfgPendTheme) - 1);
      g_cfgPendTheme[sizeof(g_cfgPendTheme) - 1] = 0;
    }
    g_cfgPendDirty = true;
  }
}

// SendSink: deliver an orchestrator reply to the owner over Telegram. Thread-safe
// queue on the device; returns false when Telegram isn't provisioned OR the reply
// queue is full, so the orchestrator can log a dropped message instead of losing it
// silently.
static bool orchSendSink(const String& chatId, const String& text) {
#ifdef NIMBUS_NOTIFIER_DEBUG
  // Mirror every orchestrator reply to serial so a `TURN` test (no Telegram) can
  // see the model's answer. chatId "serial" is the local test channel.
  Serial.printf("ORCH REPLY [%s]: %s\n", chatId.c_str(), text.c_str());
#endif
  // Console TURN channel: the reply's home IS serial - never hand it to
  // telegram::send ("serial" isn't a chat id; it burned 5 failed TLS retries
  // and lost the reply in [env:test], where the echo above is compiled out).
  if (chatId == "serial") {
#ifndef NIMBUS_NOTIFIER_DEBUG
    Serial.printf("ORCH REPLY [serial]: %s\n", text.c_str());
#endif
    return true;
  }
  // On-device voice turns (chatId "voice") route the reply to the panel, not
  // Telegram. Runs on the poll task, so hand it to the main loop via a flag (the
  // panel is main-loop-owned) under the config lock.
  if (chatId == "voice") {
    net::ConfigLockGuard lk;
    g_voiceReply = text;
    g_voiceReplyPending = true;
    return true;
  }
  // Web chat turn (POST /api/chat): capture the reply for GET /api/chat to poll.
  if (chatId == "web") {
    net::ConfigLockGuard lk;
    g_webReply = text;
    g_webReplyPending = true;
    g_webTurnDeadlineMs = 0;   // the turn answered - no longer pending
    return true;
  }
  return agent::telegram::send(chatId, text);
}

// SpeakSink: voice the `tts` device action's text. Prefer the on-device speaker
// (that is what the action promises and what the world prompt now tells the model),
// and fall back to a Telegram audio message only when on-device speech is not
// possible (no speaker / synth failed) - so the action is no longer a silent no-op
// on a device with no Telegram allowlist. Runs on the poll task between long-polls
// (single-TLS: the Telegram socket is closed), so the TTS synth + upload are safe.
static void orchSpeakSink(const String& text) {
  if (text.length() == 0) return;
  // capture=false: the tts device action records the spoken text to history itself
  // (apply.cpp captureAssistant), so speakOnDevice must not also capture it.
  if (agent::orchestrator::speakOnDevice(text, /*capture=*/false)) return;   // played on the speaker
  String allow = agent::store::telegramAllowlist();
  int c = allow.indexOf(','); String chat = (c > 0) ? allow.substring(0, c) : allow; chat.trim();
  if (chat.length() == 0) return;
  size_t n = agent::tts::synthesizeToFile(text, "/tts.mp3", "mp3");
  if (n) agent::telegram::sendMedia(chat, "audio", "/tts.mp3", "Nimbus voice");
}

// Incoming Telegram message -> one orchestrator turn (runs on the poll task, with
// the Telegram TLS socket already closed by the client).
static void orchOnMessage(const String& from, const String& chatId,
                          const String& text) {
  agent::orchestrator::handleMessage(text, from, chatId);
}

// TickCallback: advance background jobs once per poll cycle; returns active count.
static int orchTick() { return agent::orchestrator::pollJobs(); }

// Menu repaint request: the menu paints directly (bypassing the scheduler), but
// the panel takes ~2.2 s per refresh, so a burst of knob events must coalesce.
// Events set this flag; the loop flushes one paint once the menu's OWN refresh
// window (g_menuDoneAt) has elapsed - deliberately independent of the status
// render path so an in-flight/stuck status render can never stall the menu (the
// "long-press shows nothing" failure).
static bool     g_menuNeedsPaint = false;
static uint32_t g_menuDoneAt = 0;   // menu-refresh busy deadline (its own)
static uint32_t g_updCheckKickMs = 0;  // last menu "Check for updates" kick - the loop-body
                                       // reseed holds "Checking..." through the async task
                                       // spin-up instead of overwriting it with stale state
static uint8_t  g_updateAnim = 0;      // Software update indeterminate-bar phase (CUM-193)

// The owner-facing update view (CUM-193): one place maps the live OTA state to
// the status line + affordance flags, so the reseed (status line + HIL MENU?
// seam) and renderMenu (the on-screen status band) never diverge.
static nimbus::ota::UpdateView otaViewNow() {
  return nimbus::ota::updateView(
      nimbus::ota::stateFromStr(otaupd::statusStr()), otaupd::progressPct(),
      otaupd::latestSeen().c_str(), otaupd::lastError(), NIMBUS_FW_VERSION);
}
// (g_rebootPending - the deferred-reboot flag serviced at the top of loop() - is
// declared with the device-action override state above, since the orchestrator
// DeviceSink also sets it for the model's `reboot` action.)

// g_router's job table (solide::ring::Allocator) is mutated by orchEventSink() on
// the tg_poll task (core 0) under net::ConfigLockGuard. Its writes are multi-field
// and non-atomic (upsert sets used=true then fills key/status; remove clears the
// whole slot), so EVERY reader - count()/snapshot() - must take the SAME lock or it
// can observe a half-written slot or a torn count. The guard is a non-recursive
// portMUX spinlock, so these helpers must never be called while already holding it;
// callers here only take it around flag-drain/menu writes (which read no jobs).
static int jobCount() {
  net::ConfigLockGuard lk;
  return g_router.jobs().count();
}

// A live job or a top-attention call-to-action is on the ring - cosmetic overlays
// (the theme flourish) must yield to it. Reads g_router under the config lock.
static bool ringHasAttention() {
  net::ConfigLockGuard lk;
  return g_router.topAttention().active || g_router.jobs().count() > 0;
}


// Point-to-focus universe (Orchestrator mode). The Orchestrator itself is ALWAYS
// focus index 0 - the head agent you're always talking to - so the encoder never
// lands on "nothing" and SessionDetail never shows "no active session". The heavy-
// fabric sub-sessions (g_sessionList) are focus indices 1..N. (This is the on-device
// UX view only; the LLM prompt's "RUNNING SESSIONS" digest stays sub-agents-only, so
// "none running" there remains authoritative - a different axis.)
static size_t focusCount() { return 1 + g_sessionList.size(); }

// The active orchestrator host provider, for the root's label: the explicit orchHost
// override, else the first KEYED provider in the priority list (so the label matches
// the provider a turn will actually run on), else "auto".
static std::string activeHostProvider() {
  const String h = agent::store::resolvedOrchHost();
  return h.length() ? std::string(h.c_str()) : std::string("auto");
}

// Populate ScreenCtx session fields for focus index `idx`: 0 = the Orchestrator root
// (live - provider/state computed now, not snapshotted), >=1 = a sub-session snapshot.
static void fillFocus(render::ScreenCtx& c, size_t idx) {
  if (idx == 0) {
    c.sessionIsRoot   = true;
    c.sessionTitle    = "Nimbus";
    c.sessionProvider = activeHostProvider();
    c.sessionState    = g_voiceActive ? "listening" : "ready";
    return;
  }
  const auto& s = g_sessionList[idx - 1];
  c.sessionTitle    = s.title;
  c.sessionProvider = s.provider;
  c.sessionState    = s.state;
}

static std::string configUrl();      // defined below (net-derived, token-carrying)
static std::string setupUrl();       // defined below (ALWAYS the SoftAP address - P1.2)
static std::string netStatusLine();  // defined below (one-line connectivity readout)

// The header Wi-Fi glyph state (CUM-455): 2 connected, 1 saved but not connected
// (searching), 0 not set up. Notifier runs the radio OFF (Bluetooth owns the link),
// so it is always 0 there - a saved network would otherwise read as "searching"
// forever on a device that is not even trying. Shared by fillHeaderCtx and the
// debounced header-repaint watcher so the two can never disagree.
static uint8_t headerWifiState() {
  if (!g_orchMode) return 0;
  return net::staConnected() ? 2 : (net::staConfigured() ? 1 : 0);
}

// The setup SoftAP is up (a failed or stopped AP reports 0.0.0.0).
static bool softApUp() { return (uint32_t)WiFi.softAPIP() != 0u; }

// Fill the ScreenCtx fields the shared panel HEADER reads (mode / profile /
// posture + WiFi/BT glyphs + battery % + net-degraded "!"). Called from BOTH the
// status render (buildCtx) and the menu render (renderMenu) so the header is
// identical on EVERY screen - the menu path used to leave these defaulted, which
// hid the battery % and froze the glyphs at wi-/bt- (off) on all sub-menus.
static void fillHeaderCtx(render::ScreenCtx& c) {
  c.deviceName = std::string(sys::deviceName().c_str());   // top-left identity (which unit is this)
  c.modeName = (g_menu.mode() == Mode::Orchestrator) ? "orchestrator" : "notifier";
  c.posture = g_cfg.posture();
  c.profileName = profileLabel(g_cfg.profile());   // header shows the battery-mode
                                                   // vocabulary (Dark/Balanced/Full)
  // Header radio glyphs: WiFi up(2)/connecting(1)/off(0); BT linked(2)/
  // advertising(1)/off(0). BLE only runs in Notifier mode, so it's off in Orch.
  c.wifiState = headerWifiState();
  // The header Wi-Fi glyph marks setup mode (CUM-455), so the AP state rides on
  // every render - menu screens included - not just the status/setup builds.
  c.apUp = softApUp();
  c.btState   = g_orchMode ? 0
                           : (net::ble::connected() ? 2
                              : (net::ble::enabled() ? 1 : 0));
  c.networkDegraded = g_router.networkDegraded();  // header "!" marker (was never set anywhere)
  // Header L2 sound state: the ACTIVE mode's SFX level + master volume (R4).
  c.sfxLevel  = g_orchMode ? agent::store::sfxLevelOrch() : agent::store::sfxLevelNotif();
  c.sfxVolume = agent::store::sfxVolume();
  // Header L1 SD token (owner ask): in/out at a glance on every screen.
  c.sdShort = agent::memory::sdLost() ? "lost"
            : (solide::storage::available() ? "ok" : "none");
  // Battery telemetry for the header (invalid -> glyph hidden). Show the
  // BatteryModel's corrected SoC + charge state, not the raw driver percent (the
  // S3 ADC under-reads a full pack; the model calibrates + infers charging/full).
  c.battery = g_power.last();
  if (c.battery.valid) {
    c.battery.percent = g_battEstimate.percent;
    c.battery.onExternalPower = g_battEstimate.onExternalPower;
    c.battery.charging = g_battEstimate.chargeState == nimbus::power::ChargeState::Charging;
    // Hysteresis on the DISPLAYED percent: the S3 ADC (÷3.2 divider, no coulomb
    // counter) dithers the reading +/-1-2%, which would otherwise change the header
    // frame every telemetry tick and defeat the panel dirty-gate - a redundant
    // ~2.2 s refresh once a minute forever. Only move the shown value on a
    // sustained >=2-point change (0/100 always shown exactly). Purely cosmetic
    // for the header; the model's raw SoC is unchanged for analytics/logging.
    static int s_shownPct = -1;
    const int p = c.battery.percent;
    if (s_shownPct < 0 || p == 0 || p == 100 ||
        p >= s_shownPct + 2 || p <= s_shownPct - 2)
      s_shownPct = p;
    c.battery.percent = uint8_t(s_shownPct);
    // F27: the trend GLYPH (^/=/none, from charging+onExternalPower) had NO
    // hysteresis while the % beside it did - a dithering charge inference flipped
    // it every ~2 s telemetry tick, changing the header frame and defeating the
    // panel dirty-gate (a redundant ~2.2 s refresh a minute, WiFi-independent).
    // Debounce the trend pair the same way: only commit a NEW trend that has held
    // for ~3 consecutive ticks (~6 s); a real sustained transition still shows.
    static int8_t s_shownTrend = -1;   // -1 unset; 0 draining, 1 external, 2 charging
    const int8_t trend = c.battery.charging ? 2 : (c.battery.onExternalPower ? 1 : 0);
    static int8_t s_pendTrend = -1, s_pendCount = 0;
    if (s_shownTrend < 0) {
      s_shownTrend = trend;
    } else if (trend == s_shownTrend) {
      s_pendCount = 0;                 // settled back - cancel any pending flip
    } else if (trend != s_pendTrend) {
      s_pendTrend = trend; s_pendCount = 1;   // new candidate
    } else if (++s_pendCount >= 3) {
      s_shownTrend = trend; s_pendCount = 0;  // held -> commit
    }
    c.battery.charging       = (s_shownTrend == 2);
    c.battery.onExternalPower = (s_shownTrend == 1);
  }
}

// First-run posture (CUM-259): an Orchestrator device with no saved Wi-Fi that has
// not been through onboarding. In this state the idle status screen must show the
// "Set up Wi-Fi" CTA (and the loop auto-returns to Setup) so a credless owner can
// never strand off the Setup screen. Notifier has no Wi-Fi step, so it is excluded -
// its "waiting for a connection" screen is the honest resting state. The boot
// migration (setOnboarded when already provisioned) means a working device always
// reads false here, so the CTA never shows on a provisioned unit.
static bool deviceNeedsSetup() {
  return g_orchMode && !net::provisioned() && !agent::store::onboarded();
}

// Hold-to-talk status line (CUM-456): drawn on the home screen - in the on-screen
// ring, or the mic bar on a ring board - while the flow is live.
static void fillVoiceCtx(render::ScreenCtx& c) {
  if (g_voice.phase() == nimbus::voice::Phase::Idle) return;
  c.voiceTitle = g_voice.line().title;
  c.voiceDetail = g_voice.line().detail;
  c.voiceTone = uint8_t(g_voice.tone());
  c.micBusy = g_voice.busy();
}

static render::ScreenCtx buildCtx(int cursorJob) {
  render::ScreenCtx c;
  fillHeaderCtx(c);   // mode/profile/posture + WiFi/BT/battery/net-degraded header
  c.needsSetup = deviceNeedsSetup();   // StatusIdle -> first-run CTA (CUM-259)
  // Setup/QR context - filled on EVERY build (P2/P3): SetupInfo shows the AP
  // SSID + a scan-to-configure QR on unprovisioned boot, and a scheduler-driven
  // ConfigQr (the repeated-401 reaction) needs the URL without going through
  // renderMenu. Cheap string builds; renders are ~2 s events.
  c.apName = std::string(net::apSsid().c_str());
  c.apPass = std::string(net::apPass().c_str());   // per-device stored passphrase
  // (c.apUp: fillHeaderCtx above)
  c.staConnected = net::staConnected();   // locked-out ConfigQr shows AP creds (CUM-200)
  c.configUrl = configUrl();
  c.setupUrl = setupUrl();   // SetupInfo QR: always the AP address (P1.2)
  c.fwVersion = NIMBUS_FW_VERSION;   // shown small on the Setup screen
  c.netStatus = netStatusLine();
  c.cursorJob = cursorJob;
  // SessionDetail (Orchestrator): the focused agent under the encoder cursor. Index 0
  // is always the Orchestrator root; 1..N are sub-sessions (g_sessionList, main-task
  // owned - same task as this). Clamp the cursor against the full focus count.
  if (g_orchMode) {
    size_t idx = g_cursor.index();
    if (idx >= focusCount()) idx = 0;
    fillFocus(c, idx);
  }
  if (g_askOverride.length()) {
    c.askText = std::string(g_askOverride.c_str());  // mode-switch / voice screen
    c.askClosable = !g_askTransient;                 // no Close on a pre-reboot notice
    c.detailPage = g_askPage;                        // rotate pages a held reply (P2.3)
  }
  // Copy the slots under the lock into a local buffer (tiny, no heap), then build
  // the vector OUTSIDE the critical section - push_back allocates and must never run
  // under a spinlock.
  solide::ring::Slot snap[RING_MAX_SEGMENTS];
  int n;
  bool lowBatt;
  attn::Router::Attention top;
  {
    net::ConfigLockGuard lk;
    n = g_router.jobs().snapshot(snap, RING_MAX_SEGMENTS);
    lowBatt = g_router.lowBattery();
    top = g_router.topAttention();
  }
  for (int i = 0; i < n; ++i) {
    // Skip the synthetic "head" turn job on the PANEL (it stays on the ring): its
    // Running/Offline edges re-rendered the job list at the start and end of every
    // turn - two full 2.2 s panel flashes per turn, four with the synthesis turn
    // (owner: "heavy flickering while processing", 2026-07-16).
    if (g_orchMode && snap[i].key == agent::orchestrator::headJobKey()) continue;
    // nsn v2: name the session (harness + title) from the notifier Mapper, keyed by
    // segment index == job key. Empty in Orchestrator mode / on a v1 broker.
    const char* title = g_orchMode ? "" : g_notifier.mapper().titleOf(snap[i].key);
    const uint8_t harness = g_orchMode ? 0 : g_notifier.mapper().harnessOf(snap[i].key);
    c.jobs.push_back({snap[i].key, uint8_t(snap[i].status), snap[i].progress,
                      snap[i].hasAccent ? snap[i].accentHue : uint8_t(255),
                      std::string(title), harness});
  }

  // (header battery/WiFi/BT is filled by fillHeaderCtx above.)

  // BLE secure-pairing passkey for the Pairing screen. DORMANT under the active
  // Just Works config (pairingActive() never becomes true - macOS bonds with no
  // passkey); populates only if MITM is re-enabled, when the panel becomes
  // the code's channel.
  if (net::ble::pairingActive()) {
    char pk[8];
    std::snprintf(pk, sizeof pk, "%06u", unsigned(net::ble::pairingPasskey()));
    c.pairingCode = pk;
  }
  // Cloud (cumulo-nimbus) pairing: the claim code + a scannable claim URL. claimUrl
  // non-empty switches the Pairing screen to the cloud variant (see the renderer).
  if (nimbus::relay::pairingActive()) {
    c.pairingCode = nimbus::relay::claimCode().c_str();
    c.claimUrl = nimbus::relay::claimUrl().c_str();
  }

  // Badge text: low battery wins, else the top attention job's state.
  c.badgeActive = lowBatt || top.active;
  if (lowBatt) {
    c.badgeText = "LOW BATT";
  } else if (top.active) {
    switch (top.status) {
      case solide::ring::Status::AwaitingApproval: c.badgeText = "APPROVE?"; break;
      case solide::ring::Status::WaitingInput:     c.badgeText = "INPUT?";   break;
      case solide::ring::Status::Error:            c.badgeText = "ERROR";    break;
      default:                                     c.badgeText = "!";        break;
    }
  }

  // On-screen ring: a board with no physical LED ring mirrors the composited ring
  // frame onto the panel (the notifier draws it as a dot-ring). Only meaningful on
  // the colour panel; the renderer ignores ringLeds.
  if (g_screenIsTft && !solide::board().hasRing) {
    const solide::ring::RGB* rf = hw::currentRingFrame();
    const int n = hw::currentRingCount();
    c.ringLeds.resize(size_t(n));
    for (int i = 0; i < n; ++i)
      c.ringLeds[size_t(i)] = { rf[i].r, rf[i].g, rf[i].b };
    c.micHeld = g_voiceActive;   // instant pressed feedback on the hold-to-talk button
  }
  fillVoiceCtx(c);
  return c;
}

// CUM-452/453: a join screen of a provisioned device (render::joinScreenNeedsSigninCode)
// carries the hand-entry sign-in code - the 10-minute display code, the same one
// TokenDetail shows, so there is time to read it and type it. Without it the owner
// who joins the setup network meets a sign-in gate and has nothing it will accept.
// Returns whether the frame shows a code.
static bool fillJoinSigninCode(render::ScreenCtx& c, attn::ScreenId screen) {
  // "Provisioned" here is exactly "the setup network no longer signs its peers in"
  // - the same rule the web layer's token handout uses, so the two cannot disagree.
  if (!render::joinScreenNeedsSigninCode(screen, c, !net::apSignsInAutomatically()))
    return false;
  c.webToken = std::string(net::showCode().c_str());
  return true;
}

static void renderScreen(attn::ScreenId screen, int cursorJob, bool fullClear) {
  (void)fullClear;   // legacy panel refresh hint; the color panel ignores it
  const uint32_t tnow = millis();
  render::ScreenCtx ctx = buildCtx(cursorJob);
  // Outside the menu a ConfigQr is only ever the repeated-401 auto-surface, which
  // unauthenticated traffic can trigger - so it never mints or shows a code. The
  // code appears on the owner's explicit paths only: the menu's Sign-in QR
  // (renderMenu) and the Setup screen after a publish.
  const bool showsCode = screen != attn::ScreenId::ConfigQr && fillJoinSigninCode(ctx, screen);
  // Honour a dropped push. renderAndPush returns false when the previous
  // ~31 ms blit is still in flight - and it only swaps the tap map on a
  // SUCCESSFUL push, so pretending it painted leaves the panel AND the hit
  // regions a screen behind while the FSM has already moved on. Leave
  // g_lastScreen alone so the caller's entry gates still re-fire.
  const auto push = hw::tft::renderAndPush(screen, ctx);
  if (push == hw::tft::Push::Dropped) {
    g_sched.onRenderDone(tnow);   // never leave the scheduler latched
    if (showsCode) g_codeFrameDropped = true;   // the minted code never reached the glass
    return;                       // panel is a frame behind; caller retries
  }
  g_codeFrameDropped = false;
  // Pushed OR Unchanged: the panel genuinely shows this screen, so the entry
  // gates that key off g_lastScreen must see it (an Unchanged frame is a
  // SUCCESS - treating it as a drop is what latched the repaint loop).
  g_lastScreen = uint8_t(screen);
  g_panelShowsCode = showsCode;
  // First-run auto-return (CUM-259, the (a) leg): whenever a credless device lands
  // on StatusIdle, arm a short dwell after which the loop repaints SetupInfo, so a
  // tap that backed out of Setup can never leave the owner parked on the idle screen.
  // Any other screen (including SetupInfo itself) disarms it. Re-armed on each touch
  // (drainTouch) so the owner gets the full dwell from their last interaction.
  g_setupReturnAtMs = (screen == attn::ScreenId::StatusIdle && deviceNeedsSetup())
                          ? (tnow + kSetupReturnMs)
                          : 0;
  // ⚠ Release the scheduler's busy latch. g_sched.tick() sets busy_ when it
  // issues a render and clears it ONLY in onRenderDone(). A frame is ~31 ms with
  // no dwell to wait out, so it is done the moment the push returns - but if this
  // call is missed the scheduler stays busy forever and every ambient StatusIdle
  // refresh, CTA badge and detail intent silently stops after the FIRST frame.
  g_sched.onRenderDone(tnow);
#ifdef NIMBUS_TEST
  // RENDER? must follow every push, or it reports a stale frame forever and every
  // test asserting on it passes against a frozen value.
  tc::onRender(g_lastScreen, uint8_t(g_cfg.posture()), g_lastSeg, g_lastSingle,
               g_lastDark, g_lastBright);
#endif
}

// Long-press-to-talk (Orchestrator, Phase 4): record the mic, transcribe via the
// configured STT provider (Mistral Voxtral by default), and inject the transcript
// as an orchestrator turn hinting at the cursor-focused session ("[re: <id>]").
// Blocks ~4-5 s (record + STT) so the main-loop watchdog is suspended across it
// (like the console MICREC). The reply echoes on the injected chatId's sink.
// Sub-session tell/poll is unsupported, so this always talks to the ORCHESTRATOR,
// never the sub-agent directly - the '[re:]' hint is a human-style reference.
static void refreshRing();                                // fwd decls (defined below)
static void renderScreen(attn::ScreenId screen, int cursorJob, bool fullClear = false);
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
void loop() {
  esp_task_wdt_reset();
#ifdef NIMBUS_NOTIFIER_DEBUG
  // CUM-185: steady-state contiguous-SRAM sampler (test/debug builds only, so the
  // production nsn serial stream stays clean). Emits the same line as the boot
  // snaps every ~20 s, so the Orchestrator-mode steady-state intLargest floor is
  // captured on Serial even while the web server is unreachable. /api/state gives
  // the same numbers over HTTP once it binds; this is the pre-bind / soak backup.
  {
    static uint32_t s_nextSramMs = 8000;   // first sample ~8 s after boot
    if ((int32_t)(millis() - s_nextSramMs) >= 0) {
      sramSnap(g_orchMode ? "steady-orch" : "steady-notif");
      s_nextSramMs = millis() + 20000;
    }
  }
#endif
#ifdef NIMBUS_TEST
  if (g_orchMode && agent::orchestrator::testRebootRequested()) {
    agent::alog("test: staged restart (HIL persistence proof)");
    Serial.flush();
    delay(80);
    ESP.restart();
  }
#endif  // feed the F12 watchdog every iteration
  otaupd::tick();        // OTA: mark-valid once healthy + check/auto-install cadence
  otaLoopUx();           // OTA install panel/ring UX (no-op unless installing)
#if !defined(NIMBUS_TEST) && !defined(NIMBUS_NOTIFIER_DEBUG)
  usbupd::pump();        // USB serial firmware update (CUM-390): inert until the marker
#endif
  if (g_orchMode)
    agent::connectors::mcp::oauth::pump();  // advance any armed MCP OAuth flow, one
                                            // bounded TLS step (shared work arbiter)

  if (g_powerOffPending) {
    // Web "Power off" (CUM-224): the AsyncTCP task can't sleep the chip inline
    // (mode rule) so it set this flag; enter the shared clean-shutdown + deep-sleep
    // path here on the main task. Never returns.
    g_powerOffPending = false;
    enterPowerOffSleep();
  }
  if (g_factoryResetPending) {  // web/menu factory reset: scrap everything, keep only the panel identity
    g_factoryResetPending = false;   // consume the request either way (a refusal must not re-fire)
    // CUM-50 + CUM-230: factoryResetPreserveIdentity() keeps ONLY the hardware identity
    // (scrModel/tftFlip/tchCal/otaType, so a TFT board comes back on the right driver,
    // never a white screen) and seeds the setup mode so the reset device boots into the
    // Wi-Fi onboarding wizard. Everything the owner set - keys/token/bonds/config AND the
    // device name - is scrapped; the unit re-onboards fresh with a new name + mDNS.
    // g_factoryEraseSd additionally erases every private durable byte in the same
    // flow; the authoritative path list lives in agent::memory::eraseAllPrivateData().
    Serial.println(g_factoryEraseSd ? "FACTORY RESET (+SD) -> keep identity, erase config + storage, restart"
                                    : "FACTORY RESET -> keep identity, erase config, restart");
    // Progress screen with an honest duration; also buys the panel ~2.2 s to paint
    // before the erase blocks. The screen setup is preserved, so this is safe on TFT.
    g_askOverride = g_factoryEraseSd ? "Resetting to factory settings and erasing storage. Up to a minute."
                                     : "Resetting to factory settings. This takes a few seconds.";
    renderScreen(attn::ScreenId::Ask, -1);
    Serial.flush();
    if (g_factoryEraseSd && agent::memory::factoryEraseWouldRefuse()) {
      // Cheap refusal FIRST, before quiescing anything: the reseat case must
      // leave the device fully alive (poll task, durable logs) for the retry.
      // STICKY, like the OTA install refusal: without it the next ambient
      // repaint replaced this message within seconds.
      g_factoryEraseSd = false;
      Serial.println("FACTORY RESET refused -> card with memories unreachable");
      g_askOverride = "Couldn't erase storage. Reseat the SD card and try again.";
      g_askSticky = true; g_askPage = 0;
      renderScreen(attn::ScreenId::Ask, -1);
      emitMenuActionFeedback(nimbus::action::MenuAction::Reset,
                             nimbus::action::Outcome::Failed);   // error tone
    } else if (g_factoryEraseSd &&
               (agent::telegram::quiesce(7000), nimbus::errlog::setSuspended(true),
                !agent::memory::eraseAllPrivateData())) {
      // Release-gate finding 2026-10-04: the sweep used to race the live
      // tg_poll task, whose writers (chatsum/tenants persists, TTS and
      // Telegram staging audio, durable log lines - incl. the sweep's own)
      // could recreate files AFTER their tree was erased, so a handed-over
      // board could still carry the previous owner's data. The quiesce joins
      // the poll task (bounded: a turn mid-provider-call can outlive the
      // timeout, and then the erasing()/setSuspended barriers in
      // orch_persist, errlog_fs and memory_subsystem hold the line), and the
      // durable-log suspension keeps /log from being reborn mid-sweep.
      //
      // This branch: the erase returned false past the cheap check. Honest
      // copy (not the reseat line - reseating cannot fix an internal-flash
      // delete); durable logs come back on, the poll task stays down until
      // the owner retries or restarts. The memory barrier is up whenever the
      // store erase began; the one sub-path where it is not (the store
      // refused before any delete - a card demoted during the quiesce) erased
      // nothing at all, which is equally safe.
      nimbus::errlog::setSuspended(false);
      g_factoryEraseSd = false;
      Serial.println("FACTORY RESET failed mid-sweep -> a delete failed on existing data");
      g_askOverride = "Couldn't erase storage. Try again, or restart the device.";
      g_askSticky = true; g_askPage = 0;
      renderScreen(attn::ScreenId::Ask, -1);
      emitMenuActionFeedback(nimbus::action::MenuAction::Reset,
                             nimbus::action::Outcome::Failed);   // error tone
    } else {
      esp_task_wdt_reset();   // the sweep + a timed-out quiesce can near the 8s budget
      factoryResetPreserveIdentity();   // wipes NVS, keeps ONLY the hardware identity
      esp_task_wdt_reset();   // a 5-sector NVS erase + 64KB coredump erase cost ~0.5s
#if __has_include(<esp_core_dump.h>)
      // A crash dump captures task stacks, which can hold keys or message text in
      // transit; a factory-fresh device must not carry one from its previous owner.
      esp_core_dump_image_erase();      // best-effort; absent/blank partition is fine
#endif
      if (g_factoryEraseSd && !agent::memory::finalSweepPass())
        Serial.println("FACTORY RESET: final mop pass incomplete (see finalSweepPass)");
      delay(50);
      ESP.restart();
    }
  }
  if (g_sdResetPending) {  // web SD reset: erase the durable /mem store, keep config, reboot
    g_sdResetPending = false;             // consume the request either way (no re-fire)
    Serial.println("SD RESET -> erase durable store + restart");
    g_askOverride = "Erasing storage...";
    renderScreen(attn::ScreenId::Ask, -1);
    Serial.flush();
    if (agent::memory::eraseDurableStore()) {  // /mem (or /data): vectors, episodic, files, blobs
      delay(50);
      ESP.restart();                      // engines reload empty; NVS config untouched
    } else {
      // Refused: the card that held the store is gone, or a delete failed. Say so
      // honestly and DON'T reboot into a device that reads "erased" while the
      // data survives on the card. Same copy as the factory refusal.
      Serial.println("SD RESET refused -> storage not available");
      g_askOverride = "Couldn't erase storage. Reseat the SD card and try again.";
      renderScreen(attn::ScreenId::Ask, -1);
    }
  }
  if (g_sdFormatPending) {  // web full-card format: reformat the whole SD, then reboot
    g_sdFormatPending = false;            // consume the request either way (no re-fire)
    Serial.println("SD FORMAT -> reformat whole card + restart");
    g_askOverride = "Formatting storage. Up to a minute.";
    renderScreen(attn::ScreenId::Ask, -1);
    Serial.flush();
    // Reformat the ENTIRE card (not just /mem). The driver refuses cleanly with no
    // side effects when no card is mounted, so a missing card yields an honest
    // message and NO reboot - never a device that reads "formatted" over surviving
    // data. On success everything on the card is gone; reboot so the memory engines
    // reload empty (NVS config is untouched).
    using FR = solide::storage::FormatResult;
    const FR fr = solide::storage::format();
    // Ok AND RemountFailed both mean the card is already erased (mkfs succeeded),
    // so reboot either way - boot re-probes the card and the memory engines reload
    // empty; only the pre-reboot message differs. NoCard and MkfsFailed left the
    // card's data as it was, so report honestly and do NOT reboot (never claim an
    // erase that did not happen).
    if (fr == FR::Ok || fr == FR::RemountFailed) {
      g_askOverride = fr == FR::Ok ? "Storage formatted. Restarting."
                                   : "Formatted; remount failed. Restarting.";
      Serial.printf("SD FORMAT -> %s; restarting\n", solide::storage::formatResultStr(fr));
      renderScreen(attn::ScreenId::Ask, -1);
      Serial.flush();
      delay(50);
      ESP.restart();
    } else {
      const char* msg =
        fr == FR::NoCard ? "Couldn't format - storage not available" : "Couldn't format - card error";
      Serial.printf("SD FORMAT refused/failed -> %s\n", solide::storage::formatResultStr(fr));
      g_askOverride = msg;
      renderScreen(attn::ScreenId::Ask, -1);
    }
  }
  if (g_rebootPending) {  // web mode change / orchestrator reboot action
    Serial.println("REBOOT pending -> restart");
    if (g_modeSwitchTo >= 0) {
      // A WEB mode switch: give the same confirmation UX as the on-device menu path
      // (was an abrupt ~50 ms reboot with no screen/LED/sound). panel "Switching
      // to X...", the ModeSwitch sound, and the teal/amber LED sweep (which also
      // buys the ~2.2 s the panel needs to actually paint before the reset).
      const bool toOrch = (g_modeSwitchTo == 1);
      agent::memory::captureEvent("mode", String("Switching to ") +
          (toOrch ? "Orchestrator" : "Notifier") + " mode (restart follows)");
      g_askOverride = toOrch ? "Switching to Orchestrator mode..."
                             : "Switching to Notifier mode...";
      g_askTransient = true;                          // reboot follows: no Close button
      ::sfx::fire(nimbus::sfx::Ev::ModeSwitch);
      renderScreen(attn::ScreenId::Ask, -1);
      playModeSwitchFeedback(toOrch);
    }
    Serial.flush();
    delay(50);
    ESP.restart();
  }
  const uint32_t now = millis();

  // LED safety cap: 60% unless the owner/AI accepted the heat risk. Refreshed
  // every iteration (one volatile write) so a config change can't be missed.
  {
    const bool ovr = agent::store::brightOvr();
    hw::setBrightnessCap(ovr ? 255 : nimbus::power::kBrightCap);
    // Revoking the override must LOWER a live load, not just future ones (review:
    // an armed 255-bright drain otherwise burns at 255 for hours after the owner
    // turned the override off). Falling edge: re-clamp the drain in place and
    // re-apply a live model led-override through its (now-clamping) apply path.
    static bool s_prevOvr = false;
    if (s_prevOvr && !ovr) {
      if (g_highLoadActive) {
        const uint8_t want = nimbus::power::clampBright(g_drainBright, false);
        if (want != g_drainBright) {
          g_drainBright = want;
          if (!g_hlSettling && !g_thermal.tripped()) applyHighLoadRing(hlBright());
          agent::alogf("bright: override revoked mid-drain - re-clamped to %u", want);
        }
      }
      if (g_ledOverrideActive) g_devActDirty = true;   // re-apply clamped
    }
    s_prevOvr = ovr;
  }

  // --- Ring attention watchdog (fallback) ----------------------------------
  // No attention arc (red Error / CTA) may ever strand forever. The happy-path
  // reap runs on the tg_poll / broker task (orchestrator scheduleReap, notifier
  // Mapper::timeout); if THAT task is OOM-killed mid-TLS or a clearing Offline
  // is dropped, a red arc would otherwise stick for hours (observed). This runs
  // on the watchdog-fed MAIN loop - which cannot stall - and ages out any
  // attention source past AttnHoldMs + a grace, guaranteeing recovery regardless
  // of the reap path's health. Cheap (a snapshot); throttled to ~5 s.
  static uint32_t s_attnSweepAt = 0;
  if ((int32_t)(now - s_attnSweepAt) >= 0) {
    s_attnSweepAt = now + 5000;
    const uint32_t cap = uint32_t(g_cfg.effective(Param::AttnHoldMs)) + 60000;
    bool cleared, doneCleared;
    {
      net::ConfigLockGuard lk;
      cleared = g_router.forceExpireAttention(now, cap);
      // CUM-221 (the recurring stuck-ring class): also collapse a terminal Done
      // ember whose tg_poll reap (JobEngine::reapDone) never fired. Done is not an
      // attention status, so forceExpireAttention skips it - it was the one arc
      // with no always-alive backstop, which is exactly what strands lit after a
      // Telegram answer when the poll task stalls. Same generous cap.
      doneCleared = g_router.forceExpireDoneArcs(now, cap);
    }
    if (cleared) {
      agent::alogf("ring: attention watchdog force-expired a stuck arc (>%us) - reap path stalled",
                   (unsigned)(cap / 1000));
      if (g_orchMode) agent::orchestrator::noteRingBackstopFired();   // CUM-11 metric
    }
    if (doneCleared) {
      agent::alogf("ring: watchdog collapsed a stranded Done arc (>%us) - tg_poll reap stalled",
                   (unsigned)(cap / 1000));
      if (g_orchMode) agent::orchestrator::noteRingBackstopFired();   // CUM-11/CUM-221 metric
    }
    if ((cleared || doneCleared) && !g_menu.isOpen() && !voiceOwnsRing()) refreshRing();
    // CUM-243: the status-agnostic orphan reaper - collapses any ring slot whose
    // owning job the engine no longer tracks (key not in the live session set and
    // not the head), which closes the stuck-Idle / dropped-job gap the per-status
    // backstops above cannot see. Live-key snapshot is built OUTSIDE the config
    // lock: sessionInfosSnapshot() takes its own mutex and must not nest under
    // ConfigLockGuard.
    if (g_orchMode) {
      auto sessions = agent::orchestrator::sessionInfosSnapshot();
      std::vector<uint32_t> liveKeys;
      liveKeys.reserve(sessions.size());
      for (const auto& si : sessions)
        liveKeys.push_back(agent::keyFromTag(si.id.c_str()));
      bool orphanCleared;
      {
        net::ConfigLockGuard lk;
        orphanCleared = g_router.forceExpireOrphanArcs(
            liveKeys.data(), (int)liveKeys.size(),
            agent::orchestrator::headJobKey(), now, cap);
      }
      if (orphanCleared) {
        agent::alog("ring: orphan reaper collapsed an arc for a job the engine no longer tracks");
        agent::orchestrator::noteRingBackstopFired();   // CUM-243 metric
        if (!g_menu.isOpen() && !voiceOwnsRing()) refreshRing();
      }
    }
    // Head-turn reaper: the blue "processing" Running arc is NOT an attention status,
    // so forceExpireAttention above skips it. A Telegram turn whose task died leaves it
    // pulsing forever (owner bug). Free it here on the main loop.
    if (g_orchMode && agent::orchestrator::reapStuckTurn(now)) {
      agent::alog("ring: stuck-turn reaper freed a dead head-turn arc (blue processing ring)");
      g_orchRingDirty = true;
      if (!g_menu.isOpen() && !voiceOwnsRing()) refreshRing();
    }
    // W6: keep the orchestrator's own head arc lit while its sub-agents run (a
    // fan-out returns the instant it enqueues children, so the TurnGuard would
    // otherwise collapse the arc before the child arcs appear). This lights /
    // periodically refreshes / clears the arc from the always-alive main loop.
    if (g_orchMode && agent::orchestrator::reconcileHeadArc(now)) {
      g_orchRingDirty = true;
      if (!g_menu.isOpen() && !voiceOwnsRing()) refreshRing();
    }
    // Absolute working-breathe ceiling (belt-and-suspenders over reapStuckTurn):
    // if turnInFlight has been continuously true past kWorkingHardMaxMs, latch the
    // ceiling so compose() drops the "thinking" breathe - the ring can't breathe
    // "working" for hours even if the reaper is wedged. Reset the instant the flag
    // clears (a clean turn-end or the reaper), so a normal turn is never affected.
    if (g_orchMode) {
      constexpr uint32_t kWorkingHardMaxMs = 30u * 60 * 1000;   // 30 min, well above the reaper
      static uint32_t s_workingSinceMs = 0;
      const bool tif = agent::orchestrator::turnInFlight();
      if (!tif) {
        if (s_workingSinceMs != 0 || g_workingCeilingHit) { s_workingSinceMs = 0; g_workingCeilingHit = false; }
      } else {
        if (s_workingSinceMs == 0) s_workingSinceMs = now;
        if (!g_workingCeilingHit && (int32_t)(now - s_workingSinceMs) >= (int32_t)kWorkingHardMaxMs) {
          g_workingCeilingHit = true;
          agent::orchestrator::noteRingBackstopFired();   // CUM-11 metric
          agent::alog("ring: working-breathe hit its 30 min absolute ceiling - dropped (stuck-turn reaper stalled?)");
          if (!g_menu.isOpen() && !voiceOwnsRing()) refreshRing();
        }
      }
    }
  }

  // W3b active capability validation: when the owner opts into "active", refresh
  // one provider's key-verification on a slow cadence so the catalog's VERIFIED
  // marking stays honest (catches a revoked key / changed access). This reuses
  // provider_verify::request() - the SAME watchdog-safe, self-deleting, TLS-
  // arbited task the web "Verify" button uses (no new concurrency), enqueues
  // (non-blocking) one provider per wake, round-robin, spread so each keyed
  // provider refreshes about every capProbeHours. Orchestrator-only (verify needs
  // the TLS heap); a reboot resets the RAM timer (re-probes soon, harmless).
  if (g_orchMode && agent::store::capProbe() == 2 &&
      !agent::provider_verify::pending() &&
      // Never open the probe's TLS beside a live turn: with tlsSlots=2 the
      // second slot exists for VOICE beside a turn, not for an unattended probe
      // (the 78dab2c concurrent-TLS heap-collapse class). With slots=1 the
      // arbiter serializes anyway; this keeps the probe out of the queue too.
      !agent::orchestrator::turnInFlight() &&
      WiFi.status() == WL_CONNECTED) {   // a probe with no LAN only burns a -1
    // now-relative init (not a constant): a bare `= 30000` went dead for ~25
    // days once uptime crossed the int32 wrap horizon.
    static uint32_t s_nextCapProbeAt = 0;
    static bool s_capProbeInit = false;
    if (!s_capProbeInit) { s_capProbeInit = true; s_nextCapProbeAt = now + 30000; }
    if ((int32_t)(now - s_nextCapProbeAt) >= 0) {
      static int rr = 0;
      const char* provs[3] = {"openai", "anthropic", "mistral"};
      bool keyed[3] = {agent::store::hasOpenaiKey(), agent::store::hasAnthropicKey(),
                       agent::store::hasMistralKey()};
      int keyedCount = (keyed[0] ? 1 : 0) + (keyed[1] ? 1 : 0) + (keyed[2] ? 1 : 0);
      for (int i = 0; i < 3; i++) {
        int idx = (rr + i) % 3;
        if (keyed[idx]) { agent::provider_verify::request(provs[idx]); rr = idx + 1; break; }
      }
      // Spread the interval so each keyed provider is refreshed ~every capProbeHours.
      uint32_t stepMs = (uint32_t)agent::store::capProbeHours() * 3600000u /
                        (uint32_t)(keyedCount > 0 ? keyedCount : 1);
      if (stepMs < 60000) stepMs = 60000;       // never hammer faster than 1/min
      s_nextCapProbeAt = now + stepMs;
    }
  }

  // CUM-447: re-arm a low-memory-deferred provider verify when its backoff comes
  // due. Self-gated (online, no turn in flight, internally throttled) and reuses the
  // same self-deleting, TLS-arbited verify task as the capProbe tick above - no new
  // task, no new TLS slot. Runs in either mode (deferrals bite hardest in Notifier).
  agent::provider_verify::pumpRetry();

  // Auto-revert a POST /api/preview once its window elapses: nothing else
  // necessarily calls refreshRing() again on its own, so this is the one place
  // that proactively drops back to the live composed state.
  if (g_previewActive && int32_t(now - g_previewUntil) >= 0) {
    g_previewActive = false;
    if (!g_menu.isOpen()) refreshRing();
  }

  // Pump the captive DNS / mDNS and apply any staged web config on the main task.
  // Orchestrator-only: in Notifier the radio (and the web server) never came up.
  if (g_orchMode) {
    net::process();
    net::loopWeb();
    // CUM-207: drive the multi-network failover supervisor inline (no task). It stays
    // passive unless the link is genuinely lost with a second saved network to try.
    net::link::tick(now, g_orchMode, agent::store::onboarded());
  }
#ifdef NIMBUS_TEST
  // ── HOST DEAD-MAN CHECK (battlab) ─────────────────────────────────────────
  // A host-driven campaign drain must be refreshed by its host. If the host dies,
  // restarts, sleeps, or the network drops, NOTHING else stops the ~1.5 A load and
  // the pack runs FLAT (killed a pack live, 2026-07-16). This is the ONLY thing
  // that fails the load safe on its own.
  // Placement is deliberate and load-bearing:
  //   • 2-space indent = mode-agnostic. The thermal poll AND the settle machine are
  //     trapped inside `if (g_orchMode)` below, so in Notifier mode this is the ONLY
  //     watcher of the load. It must never join them in there.
  //   • immediately after loopWeb() - that is what drains a just-arrived keepalive
  //     into drainSet(), so a refresh landing this pass is honoured this pass.
  //   • keys ONLY on g_highLoadActive + the ttl. NOT on ring brightness: the settle
  //     machine legitimately darkens the ring for 9 s every 15 min, and hlBright()
  //     returns 0 while thermally tripped - dark != off.
  //   • g_storageTargetMv == 0 gates it to a campaign drain; STORAGE is a production
  //     op with no host and its own voltage auto-stop.
  //   • unsigned-difference compare = millis()-rollover correct.
  if (g_highLoadActive && g_drainTtlMs && g_storageTargetMv == 0 &&
      uint32_t(millis() - g_drainRefreshedMs) >= g_drainTtlMs) {
    const unsigned aliveS = unsigned(g_drainTtlMs / 1000u);
    drainSet(false, false);              // full stop: ring released, guard disarmed
    agent::alogf("drain: HOST DEAD-MAN expired (no refresh for %us) - load OFF, "
                 "pack protected", aliveS);
  }
#endif
  // A web theme switch asks for an immediate ring re-compose so the new colour
  // shows on the device instantly (not only at the next ring event).
  if (net::consumeRingRefresh() && !g_menu.isOpen()) refreshRing();

  // CUM-452: the setup network was just published (web button or device menu).
  // Radio-only feedback left the owner with nothing on the device, and the web page
  // that showed a toast went unreachable a second later. Put the Setup screen up -
  // network name, password, join QR and, on a provisioned device, the sign-in code
  // the setup network's page will ask for. Runs BEFORE the LED confirm below: a
  // publish closes an open menu, and the confirm only plays with the menu closed.
  if (net::consumeSetupInfoRequest() || g_setupInfoReq) {
    g_setupInfoReq = false;
    showSetupAfterPublish(now);
  }
  // ...and give the panel back once the Setup screen has done its job: Wi-Fi came
  // back (joining resumed, or a network was joined) or the hold elapsed. The network
  // password and a live sign-in code must not stay on the glass indefinitely, and
  // the screensaver only arms from the status screen.
  if (g_setupHoldUntilMs) {
    const bool sta = net::staConnected();
    if (!sta) g_setupHoldSawStaDown = true;   // the publish has taken the link down
    if ((sta && g_setupHoldSawStaDown) || int32_t(now - g_setupHoldUntilMs) >= 0) {
      g_setupHoldUntilMs = 0;
      if (!g_menu.isOpen() && g_lastScreen == uint8_t(attn::ScreenId::SetupInfo)) {
        renderScreen(attn::ScreenId::StatusIdle, -1);
      } else if (g_menu.showingCodeFromSetup()) {
        // The enlarged code opened from Setup ends with Setup: a live sign-in code
        // must not outlast the hold on the glass (the view re-mints on its own).
        g_menu.close();
        settleMenuAfterMutation(now);
      }
    }
  }
  // P3: subtle LED confirmation for web actions (WiFi saved / scan done) - a
  // short theme-accent soft-pulse window, then restore the composed ring. (Was
  // Pattern::Flash - 3 hard full-ring ON/OFF snaps; ambient grammar, owner
  // 2026-07-16: even one-shot confirms swell, they don't strobe.) Respects
  // every LED silence: never in Dark posture, lights-off, or over a model-
  // painted ring, and never while the menu owns the interaction.
  if (net::consumeLedConfirm() && !g_menu.isOpen() && !g_lightsOff &&
      !g_ledOverrideActive && g_cfg.posture() != Posture::Dark) {
    nimbus::ThemeColor th =
        nimbus::themeAccent(std::string(agent::store::theme().c_str()));
    solide::leds::clearFrame();   // exit any raw frame so the pattern shows
    solide::leds::show(solide::leds::Pattern::Pulse, th.r, th.g, th.b);
    g_ledConfirmUntilMs = now + 1200;
  }
  if (g_ledConfirmUntilMs != 0 && int32_t(now - g_ledConfirmUntilMs) >= 0) {
    g_ledConfirmUntilMs = 0;
    // Restore the ring the confirm swell borrowed. A menu-action confirm can fire
    // while the menu is OPEN (the whole point - the ring must speak on a dead
    // panel), so restore the menu's own ring baseline there (dim echo on the
    // encoder, dark on a touch panel) instead of leaving the Pulse lit forever;
    // otherwise recompose the composed status ring.
    if (g_menu.isOpen()) {
      if (!g_screenIsTft || g_menu.adjustingValue()) menuRingRepaint(true);
      else                                           solide::leds::off();
    } else {
      refreshRing();   // menu/override may have taken the ring mid-window
    }
  }
  // The menu-action toast line is transient: once its window elapses, repaint the
  // menu so the help pane returns to its normal text.
  if (g_menuToastUntilMs != 0 && int32_t(now - g_menuToastUntilMs) >= 0) {
    g_menuToastUntilMs = 0;
    g_menuToast.clear();
    if (g_menu.isOpen()) g_menuNeedsPaint = true;
  }

  // P3: repeated web-auth failures (3 x 401 / 60 s) - someone is on a token-less
  // config page, so surface the Config QR on the panel unprompted (buildCtx
  // carries configUrl on every render since P2). Foreground menu wins. Held
  // TRANSIENTLY (kAuthQrHoldMs) so a bad-token poller can't park the panel here.
  if (net::consumeAuthQrRequest() && !g_menu.isOpen() &&
      g_lastScreen != uint8_t(attn::ScreenId::Screensaver)) {
    // (The request is consumed either way; we just don't clobber a deep-idle
    // logo with a QR meant for a user who is plausibly present at live status.)
    renderScreen(attn::ScreenId::ConfigQr, -1);
    g_authQrUntilMs = now + kAuthQrHoldMs;
  }
  // Auth-QR hold elapsed: fall back to ambient status (unless the menu is now
  // deliberately showing the QR, or a later screen already replaced it) so the
  // panel returns to idle and the screensaver can arm.
  if (g_authQrUntilMs && int32_t(now - g_authQrUntilMs) >= 0) {
    g_authQrUntilMs = 0;
    if (!g_menu.isOpen() && g_lastScreen == uint8_t(attn::ScreenId::ConfigQr))
      renderScreen(attn::ScreenId::StatusIdle, -1);
  }

  // Resistive touch liveness (FIX 4): self-rate-limited (~2 s), resistive-only.
  serviceTouchLiveness(now);

  // Colour-panel controller liveness (honest display verdict): self-rate-limited
  // (~2 s) and idle-bus-gated inside. Reads the controller id so the health row
  // and /api/state report a panel that has gone off the SPI bus as a fault
  // instead of the boot begin() result's hardwired "up" (the owner's black glass).
  if (g_screenIsTft) hw::tft::pollControllerLiveness(now);

  // One-shot boot panel beacon (CUM-388): once the liveness verdict has settled,
  // emit the loud "wrong variant / dead panel" line + machine token, or confirm
  // the panel is up. Runs unconditionally (an init-failed panel leaves g_screenIsTft
  // false, and that case must still be surfaced).
  emitBootPanelSignalOnce(now);

  // Battery: sample + two-threshold policy at a low cadence. Inert with
  // NullMonitor (no hardware). T1 raises a low-battery badge through the SAME
  // attention Router as job attention and forces the Battery Saver profile;
  // recovery/VBUS re-resolves the profile; T2 persists + clean deep-sleeps
  // (waking on VBUS when the sense pin exists).
  if (uint32_t(now - g_lastPowerTick) >= 2000) {
    g_lastPowerTick = now;
    // Owner control over the T1 battery-mode switch, re-synced every tick (NOT
    // inside the telemetry gate below, which fires only every 60-300 s - a toggle
    // must not appear inert for minutes).
    g_power.setAutoSaverOnLow(agent::store::lowBattSaver());
    power::ManagerActions pa = g_power.tick(now);
    // Honest open-sense-line telemetry: fold this reading into the debounced
    // detector on its OWN validity-independent cadence. It must NOT live inside
    // the telemetryDue block below - that fires only on VALID samples, which
    // starved the detector on the one board it was built for (open divider =
    // invalid every tick, so "desk-powered" was shown forever). A valid sample
    // still clears it at once.
    if (pa.senseTelemetryDue) g_senseMissing.update(battMonOn(), g_power.last().valid);
    // Re-resolve the ACTIVE profile (forced > VBUS > user) into g_cfg so the
    // presets take effect live. The user's authoritative pick lives in the
    // selector (g_selector.user()) and is what persistConfig() stores - this
    // only ever mutates the transient active profile, never the stored pick.
    // Suppressed while the menu is open: there g_cfg.profile() holds the pick the
    // user is editing (seeded from g_selector.user() on open), and clobbering it
    // with resolve() would corrupt the in-progress edit. The active profile is
    // re-resolved when the menu closes.
    // ⚠ LEVEL-triggered, not edge-triggered. pa.profileChanged is the OR of four
    // EDGES (enter/exit T1, VBUS connect/disconnect), so gating on it meant that
    // toggling "save power when low" while a T1 warning was ALREADY latched did
    // nothing until the next edge - possibly hours, and indistinguishable from a
    // broken setting. Comparing against resolve() is idempotent and subsumes the
    // edge form: outside the menu, g_cfg.profile() == g_selector.resolve() always
    // holds (boot seeds it and every mutation path re-resolves).
    if (!g_menu.isOpen() && g_cfg.profile() != g_selector.resolve()) {
      g_cfg.setProfile(g_selector.resolve());  // forced > VBUS > user
      applyConfig();                            // live; transient, not persisted
    }
    if (pa.warnT1 || pa.clearedT1) {
      attn::Event be;
      be.type = pa.warnT1 ? attn::Event::Type::LowBattery
                          : attn::Event::Type::BatteryOk;
      be.value = g_power.last().percent;
      attn::Decision d;
      { net::ConfigLockGuard lk; d = g_router.route(be, now); }
      if (!g_menu.isOpen()) {
        refreshRing();
        if (d.screen.render) g_sched.onIntent(uint8_t(d.screen.id), d.screen.attention, now);
      }
      // The ping itself fires below, AFTER the telemetry block has refreshed
      // g_battEstimate - the message reports the calibrated scale, and on the
      // first tick both warnT1 and telemetryDue are due in the same pass.
    }
    if (pa.telemetryDue) {
      // Feed the analytics model + snapshot the estimate for the web layer. Persist
      // the learned state only when a discharge segment completed (NVS wear) - the
      // learning that must survive a reboot.
      // ⚠ Pass the drain/storage harness state: a synthetic LED load (up to ~1.5 A vs
      // the device's normal idle draw) must NEVER teach the rate EWMA or the health
      // baselines - those describe NORMAL use and persist to NVS. Without this a curve
      // run leaves the device predicting hours-from-full forever (live-caught on Board 2
      // after the 5.75 h campaign: ~17 %/hr learned => ~4-6 h projected from a full pack).
      const bool artificialLoad = g_highLoadActive || g_storageTargetMv != 0;
      g_battModel.update(now, g_power.last(), artificialLoad);
      g_battEstimate = g_battModel.estimate();
      // Persist when a discharge segment completed OR the full-charge anchor moved
      // (an owner BATTCAL/api-battcal or an auto-learned plateau) - else an auto-
      // learned anchor never closing a segment is lost on reboot and two identical
      // boards drift apart in displayed % (one calibrated, one not).
      if (g_battEstimate.segments != g_battSavedSegments ||
          g_battModel.fullAnchorMv() != g_battSavedAnchor)
        saveBattModel();
      // Durable SD discharge log (only while actually draining - bounds growth +
      // is the data the model learns from). No-op with no card / while demoted.
      if (g_battEstimate.chargeState == nimbus::power::ChargeState::Discharging &&
          g_power.last().valid)
        agent::memory::appendBatteryHistory(agent::memory::nowHours(),
                                            g_power.last().millivolts, g_battEstimate.percent,
                                            nimbus::power::chargeStateStr(g_battEstimate.chargeState));
      // Only repaint StatusIdle if it's the LIVE screen - else the telemetry tick
      // yanks the user off a JobDetail / SessionDetail they're reading (same guard
      // the WiFi/BT header-refresh path below already uses; this one was missing it).
      if (!g_menu.isOpen() && g_lastScreen == uint8_t(attn::ScreenId::StatusIdle))
        g_sched.onIntent(uint8_t(attn::ScreenId::StatusIdle), false, now);
    }
    // Low-battery owner ping, gated by the AlertGate: fires at <=20% CALIBRATED
    // charge while discharging (owner 2026-08-12 - NOT the raw T1 edge, which
    // lands around ~45% real), at most one per cooldown window even across the
    // T2 sleep's 5-minute wake-sniff boots (the persisted epoch survives them).
    // External power re-arms. Runs on the telemetry tick, right after the block
    // above refreshed g_battEstimate.
    if (g_battEstimate.onExternalPower) g_lowBattGate.noteExternalPower();
    if (pa.telemetryDue && g_orchMode && g_cfg.effective(Param::TgLowBattPing) &&
        g_lowBattGate.shouldPing(
            g_battEstimate.percent,
            g_battEstimate.chargeState == nimbus::power::ChargeState::Discharging,
            (uint32_t)time(nullptr)))
      lowBatteryPing();
    if (g_lowBattGate.persistEpoch() != g_lowBattSavedPingEp) {
      g_lowBattSavedPingEp = g_lowBattGate.persistEpoch();
      agent::store::setLowBattPingEpoch(g_lowBattSavedPingEp);
    }
    // A DEEP drain deliberately suppresses the clean T2 shutdown so the pack runs to the
    // real cutoff (the campaign wants the full curve). Only reachable via the TEST-only
    // DRAIN command; STORAGE (g_drainDeep=false) + production always honor T2.
    // Live-sync the runtime-configurable protection each power tick, so a web/AI
    // change to sleepMv/sleepOvr applies within one tick with no extra plumbing.
    if (pa.telemetryDue) {
      g_power.policyRef().setT2PackMv(agent::store::sleepMv());
      if (g_power.policyRef().t2Override() != agent::store::sleepOvr())
        g_power.policyRef().setT2Override(agent::store::sleepOvr());
    }
    // ⚠ the grace-pending gate is load-bearing (review, CRITICAL): deep sleep wipes
    // the policy's RAM state, so after a wake the debounce re-fires ~8 s into the
    // boot - long before the grace window's own check ever ran. Without this gate
    // the "90 s to react" was dead code and every timer/charger wake re-slept in ~10 s.
    const bool gracePending = s_wokeFromLowBatt && s_lowBattGraceUntil != 0;
    if (pa.shutdownT2 && !gracePending &&
        !(g_highLoadActive && g_drainDeep) && !agent::store::sleepOvr()) {
      agent::alogf("power: pack at/below %umV (debounced) - deep sleep "
                   "(charge to wake)", unsigned(agent::store::sleepMv()));
      enterLowBattSleep();
    }
  }

  // A low-battery WAKE gets a grace window (glance at the screen, plug a charger,
  // set the override via web/AI), then decides via the WAKE BAR - not the sleep
  // threshold. A drained pack RESTS UPWARD (measured: 6918-6992 mV after hitting
  // the 6000 floor), so "above sleepMv?" oscillates sleep->rest->wake->drain->
  // sleep forever (owner-observed on Board 2). stayAwakeAfterSleep() demands
  // wakeMv (default 7200, above any rested-empty reading) or a positive charging
  // inference; the reading is taken FRESH (g_power.last() can be minutes stale
  // at battery-saver telemetry cadence).
  if (s_wokeFromLowBatt && s_lowBattGraceUntil && now > s_lowBattGraceUntil) {
    s_lowBattGraceUntil = 0;
    const power::Sample fresh = g_monitor ? g_monitor->sample() : power::Sample{};
    const bool charging = fresh.onExternalPower ||
                          g_battEstimate.chargeState == power::ChargeState::Charging ||
                          g_battEstimate.chargeState == power::ChargeState::Full;
    const bool stay = power::stayAwakeAfterSleep(
        fresh.valid ? fresh.millivolts : 0, agent::store::sleepMv(),
        agent::store::wakeMv(), charging);
    if (!stay && !agent::store::sleepOvr() && !(g_highLoadActive && g_drainDeep)) {
      agent::alogf("power: %umV after the wake grace < wake bar %umV - back to sleep",
                   unsigned(fresh.millivolts), unsigned(agent::store::wakeMv()));
      enterLowBattSleep();   // noreturn
    }
    if (stay)
      agent::alogf("power: recovered (%umV >= %umV%s) - staying awake",
                   unsigned(fresh.millivolts), unsigned(agent::store::wakeMv()),
                   charging ? " / charging" : "");
    else
      agent::alogf("power: below the wake bar but override/drain active - staying awake");
    g_power.policyRef().clearT2();   // drop any latched decision from stale state
    s_wokeFromLowBatt = false;
  }

  // SD graceful degradation: an adaptive liveness probe demotes the memory tier
  // when a card that was present at boot vanishes (cold joint / pull) and promotes
  // it back on recovery - all WITHOUT a reboot (episodic appends fall to the RAM
  // ring, vectors re-cap). The tick self-rate-limits; the edge drives the cue.
  {
    static bool s_prevSdLost = false;
    agent::memory::tickSdHealth(now);
    const bool lost = agent::memory::sdLost();
    if (lost != s_prevSdLost) {
      s_prevSdLost = lost;
      agent::alogf("main: SD %s", lost ? "lost -> degraded (no reboot)" : "recovered -> SD tier");
      ::sfx::fire(lost ? nimbus::sfx::Ev::NetDegraded : nimbus::sfx::Ev::NetOk);
      // Timeline row. The "lost" row lands RAM-ring-only by definition (the SD
      // just vanished); the recovery row is durable - together they bracket the
      // degraded window for "what happened?" queries.
      agent::memory::captureEvent("sd", lost
          ? "SD card lost - memory demoted to RAM tier (no reboot)"
          : "SD card recovered - memory promoted back to SD tier");
    }
  }

  // Header BT/WiFi status glyphs are computed at render time (buildCtx), so they
  // go stale when the link state changes with no other event to repaint - the
  // classic case being WiFi/BLE coming up a few seconds AFTER boot, leaving the
  // status screen frozen on "wi- bt-". Detect a real change in the glyph levels
  // and schedule a coalesced StatusIdle repaint, but only while StatusIdle is the
  // live screen so this never yanks away a JobDetail / menu / pairing view.
  // DEBOUNCED (~2.5 s): the raw levels can flap with no real news - the BLE
  // glyph when WiFi-reconnect scans starve the shared 2.4 GHz radio and the
  // broker link drops/relinks every few seconds, and (before staConfigured()
  // was fixed to read stored config) the WiFi glyph on every retry. Each flap
  // repainted StatusIdle - a real panel refresh per bounce. A change must now
  // hold for the debounce window before it repaints; a boot-time link-up still
  // shows within ~2.5 s.
  {
    static int s_lastWifi = -1, s_lastBt = -1;
    static int s_pendWifi = -2, s_pendBt = -2;
    static uint32_t s_pendSinceMs = 0;
    // The Wi-Fi glyph level plus its "AP" setup-mode marker (CUM-455): the marker
    // appearing or clearing is a visible header change too, so it is folded into
    // the watched value (levels are 0..2, so +kApMarker keeps every pair distinct).
    constexpr int kApMarker = 10;
    const int wl = headerWifiState();
    const int w = wl + (render::wifiApMarker(uint8_t(wl), softApUp()) ? kApMarker : 0);
    const int b = g_orchMode ? 0
                             : (net::ble::connected() ? 2
                                : (net::ble::enabled() ? 1 : 0));
    if (w == s_lastWifi && b == s_lastBt) {
      s_pendWifi = -2; s_pendBt = -2;            // settled back - cancel pending
    } else if (w != s_pendWifi || b != s_pendBt) {
      s_pendWifi = w; s_pendBt = b; s_pendSinceMs = now;   // new candidate
    } else if (now - s_pendSinceMs >= 2500) {    // held stable -> commit + repaint
      s_lastWifi = w; s_lastBt = b;
      s_pendWifi = -2; s_pendBt = -2;
      if (!g_menu.isOpen() &&
          g_lastScreen == uint8_t(attn::ScreenId::StatusIdle))
        g_sched.onIntent(uint8_t(attn::ScreenId::StatusIdle), false, now);
      // The Setup screen after a publish carries the same header (CUM-455): it is
      // painted in the very pass that drops the link, before the radio reports it,
      // so repaint it once the new level has settled.
      else if (!g_menu.isOpen() && g_lastScreen == uint8_t(attn::ScreenId::SetupInfo))
        renderScreen(attn::ScreenId::SetupInfo, -1);
    }
  }

  // While the Software update submenu is showing, reseed its live status line
  // (~1 Hz) from the OTA engine so Checking../Up to date/Update found appear
  // WITHOUT any encoder event. Lives at loop-body scope (like the header
  // watcher above) - it used to sit inside the encoder-event pump, where it
  // only ever ran on knob motion, so an untouched knob never showed the check
  // result (prism v3.1.0 finding). The kick-grace guard keeps the drain's
  // "Checking..." on screen through the async checkTask spin-up instead of
  // overwriting it with the PRE-check state.
  if (g_menu.isOpen() && g_menu.showingUpdate()) {
    static uint32_t s_lastUpdSeed = 0;
    if (now - s_lastUpdSeed > 1000) {
      s_lastUpdSeed = now;
      const std::string st = otaupd::statusStr();
      const bool kickGrace = g_updCheckKickMs &&
                             (now - g_updCheckKickMs < 2500) && st != "checking";
      if (!kickGrace) {
        // One mapping for the line + affordances (CUM-193); the on-screen band
        // in renderMenu reads the same view.
        const nimbus::ota::UpdateView uv = otaViewNow();
        if (uv.showInstall)
          g_menu.setUpdateAvailable(std::string(otaupd::latestSeen().c_str()));
        if (uv.busy) g_updateAnim++;   // slide the indeterminate progress block
        if (!(st == "idle" && !g_updCheckKickMs)) {  // never blank the pre-check help
          g_menu.setUpdateStatus(uv.line);
          g_menuNeedsPaint = true;
        }
      }
    }
  }

  // Keep the on-screen Sign-in QR live (CUM-209). The Sign-in QR encodes a single-
  // use code with a TTL; the menu paints only on knob events, so a QR left on the
  // screen would keep showing a code that silently expires (a later scan then 401s).
  // While the ConfigQr screen is showing, ask for a repaint once the code goes stale
  // - renderMenu() -> configUrl() -> panelSigninCode() then re-mints it, so the QR
  // rotates ~once per TTL-window rather than per frame. Cheap poll (a millis compare).
  if (g_menu.isOpen() && g_menu.showingConfigQr() && net::panelCodeStale())
    g_menuNeedsPaint = true;

  // Keep the on-screen "Show code" sign-in code honest (CUM-295). The hand-entry
  // code carries a 10-minute display TTL; while TokenDetail is open we (a) mint a
  // fresh window on ENTRY unless the current code still has most of its life,
  // (b) repaint ~1 Hz so the mm:ss countdown ticks, and (c) re-mint + repaint the
  // moment it stops working (expired, redeemed, evicted), so a dead code never sits
  // on screen as if valid. renderMenu() reads net::showCode()/showCodeSecsLeft(), so
  // a repaint is what actually re-mints and re-ticks.
  {
    static bool     s_tokenDetailWasOpen = false;
    static uint32_t s_tokenDetailTickMs = 0;
    const bool tdOpen = g_menu.isOpen() && g_menu.showingTokenDetail();
    // On ENTRY keep a code with at least half its window left: TokenDetail is also
    // "tap the code to see it bigger" from the Sign-in QR's join screen (CUM-453),
    // and it must show the same digits the owner may already be typing. An older
    // code gets a fresh full window, as before.
    constexpr uint32_t kKeepOnEntryS = nimbus::SigninCodes::DISPLAY_TTL_MS / 2000;
    const bool entry = tdOpen && !s_tokenDetailWasOpen;
    if (tdOpen && (net::showCodeStale() || (entry && net::showCodeSecsLeft() < kKeepOnEntryS))) {
      net::showCodeRemint();
      g_menuNeedsPaint = true;
      s_tokenDetailTickMs = now;
    } else if (tdOpen && int32_t(now - s_tokenDetailTickMs) >= 1000) {  // ~1 Hz tick
      g_menuNeedsPaint = true;
      s_tokenDetailTickMs = now;
    }
    s_tokenDetailWasOpen = tdOpen;
  }

  repaintIfShownCodeDead();

  // Flush a coalesced menu repaint once the menu's OWN refresh window elapses.
  // Gated on g_menuDoneAt so a busy/stuck status render can
  // never stall the menu: g_menuDoneAt only ever tracks the previous MENU frame,
  // which is elapsed in the common open case, so this fires on the next loop
  // (~3 ms) and the menu appears within one refresh. When a menu frame is still
  // streaming, it waits for that frame (protecting g_menuFb), never for status.
  if (g_menu.isOpen() && g_menuNeedsPaint && int32_t(now - g_menuDoneAt) >= 0)
    renderMenu();
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
